cyborgcnc/CYBORGCNC__RRVC3MOD/500x500/MARCEL-Remix-MODS/Top-Lid/README.md

<p align="center">
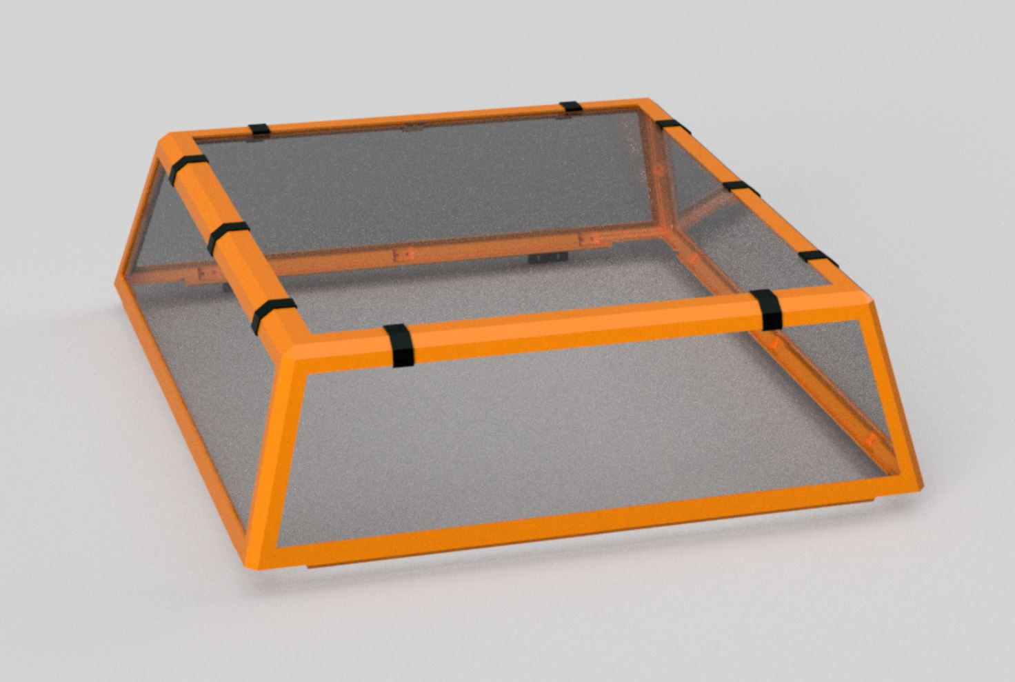
[picture p42: 500x500/MARCEL-Remix-MODS/Top-Lid/500_TopLid.JPG]

</p>
