cyborgcnc/CYBORGCNC__RRVC3MOD/400x400/HCOMB-Russel-Remix/IMG_20210630_090853.JPG

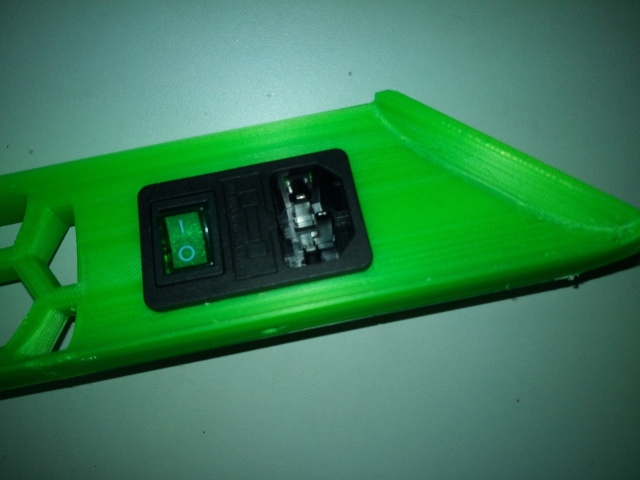
400x400/HCOMB-Russel-Remix/IMG_20210630_090853.JPG
