cyborgcnc/CYBORGCNC__RRVC3MOD/Activated-Carbon-Filter/Filter1.JPG

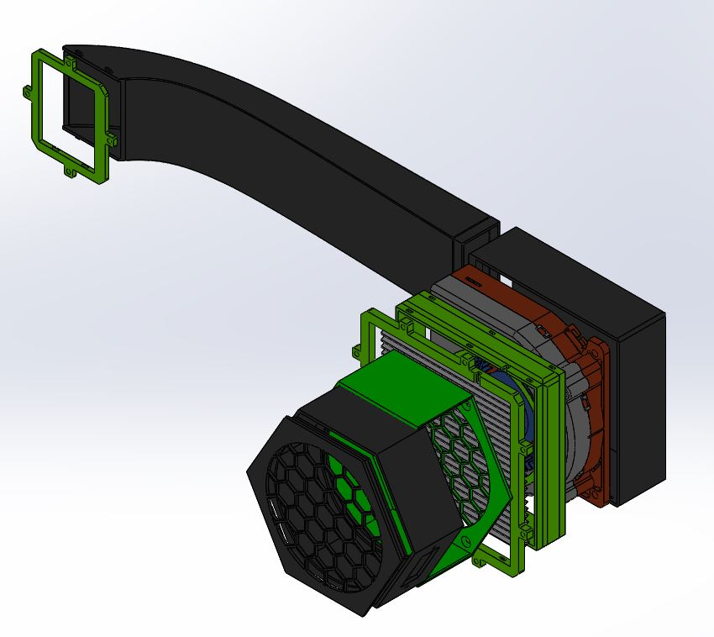
Activated-Carbon-Filter/Filter1.JPG
