cyborgcnc/CYBORGCNC__RRVC3MOD/Activated-Carbon-Filter/Filter3.JPG

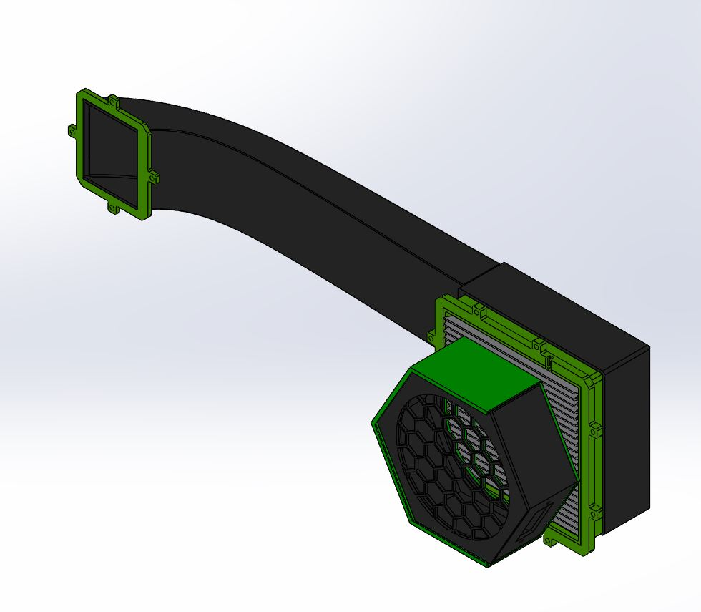
Activated-Carbon-Filter/Filter3.JPG
