cyborgcnc/CYBORGCNC__RRVC3MOD/CAN_Bus/SHT42.jpg

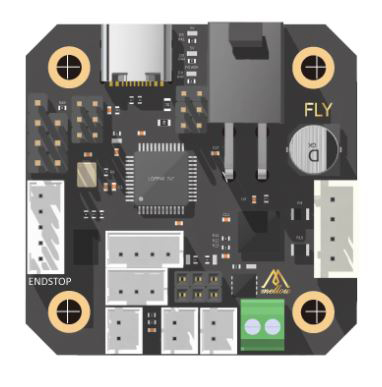
CAN_Bus/SHT42.jpg
