cyborgcnc/CYBORGCNC__RRVC3MOD/SpoolHolder-Inside/IMG_7930.jpg

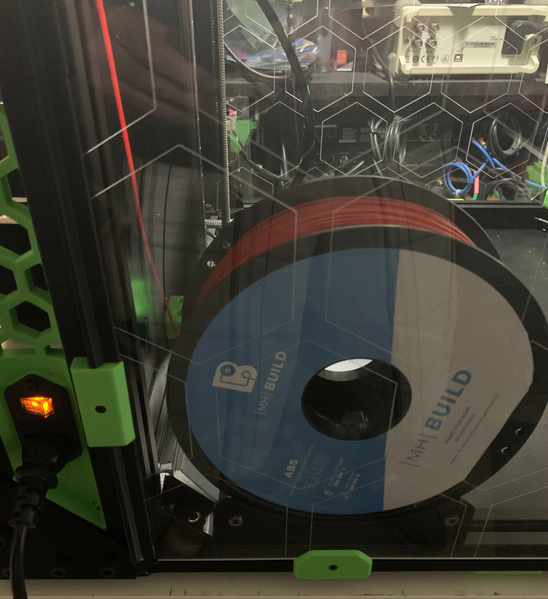
SpoolHolder-Inside/IMG_7930.jpg
