cyborgcnc/CYBORGCNC__RRVC3MOD/SpoolHolder-Inside/Spool2.JPG

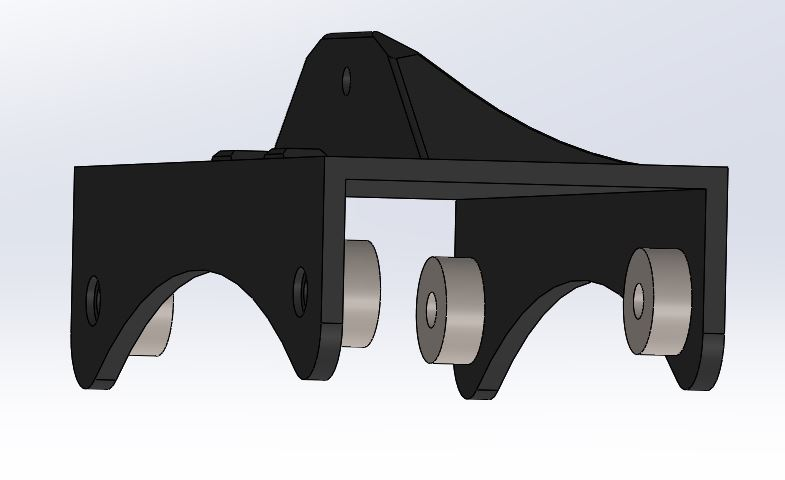
SpoolHolder-Inside/Spool2.JPG
