cyborgcnc/CYBORGCNC__RRVC3MOD/SpoolHolder-Inside/Spool4.JPG

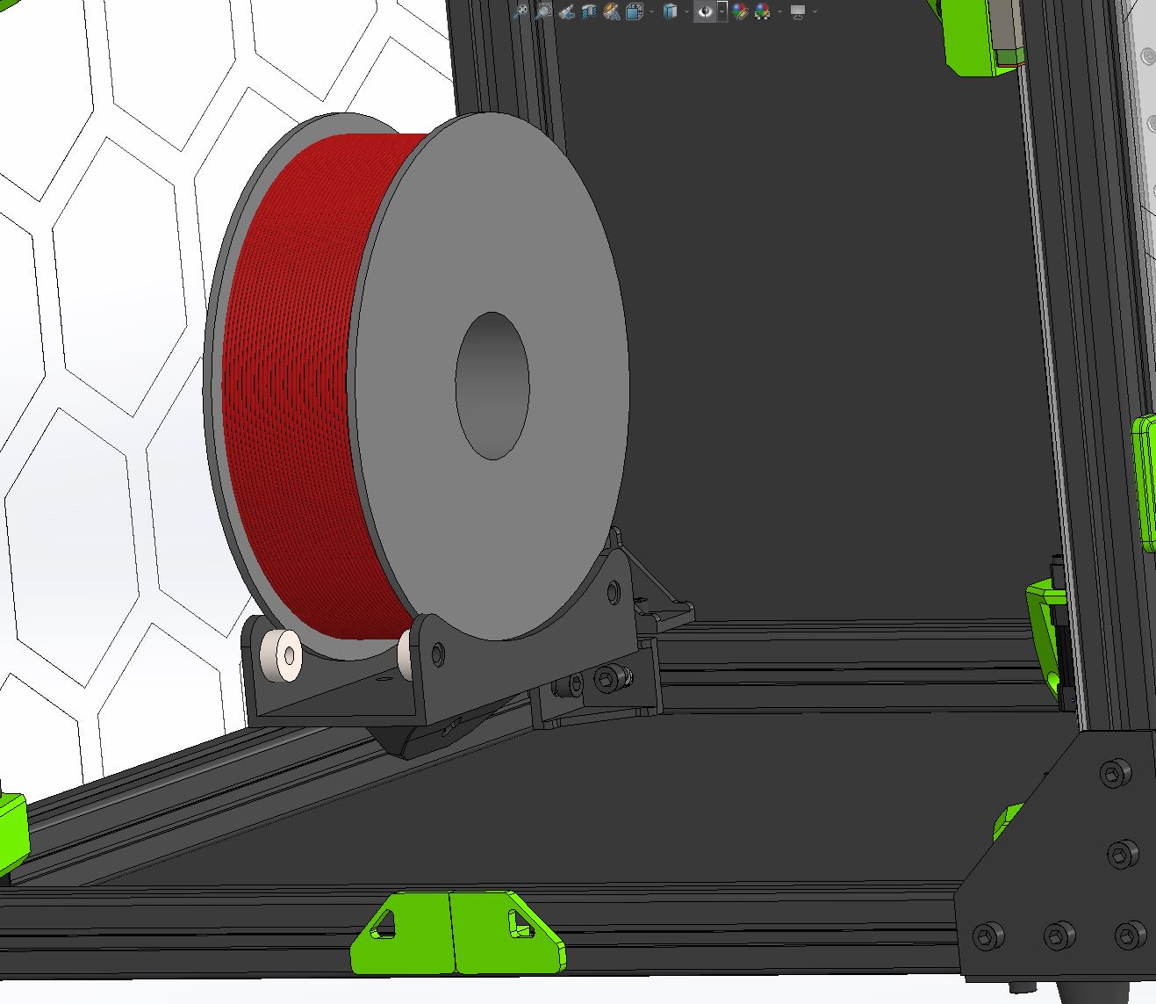
SpoolHolder-Inside/Spool4.JPG
