cyborgcnc/CYBORGCNC__RRVC3MOD/Activated-Carbon-Filter/Air-Duct-Internal.STEP

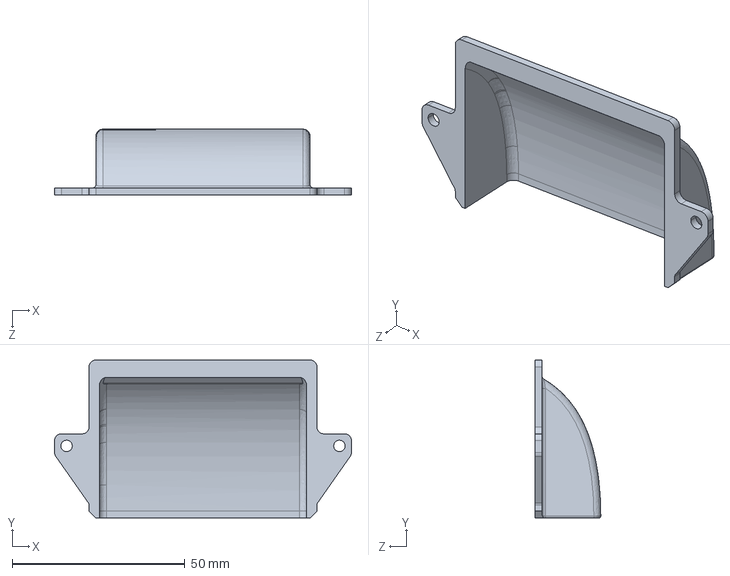
[picture p65: CAD file, 2022-03-03]
Activated-Carbon-Filter/Air-Duct-Internal.STEP
86.0 x 45.7 x 19.0 mm
