cyborgcnc/CYBORGCNC__RRVC3MOD/CAN_Bus/Cable-Holder-V4.STEP.STL

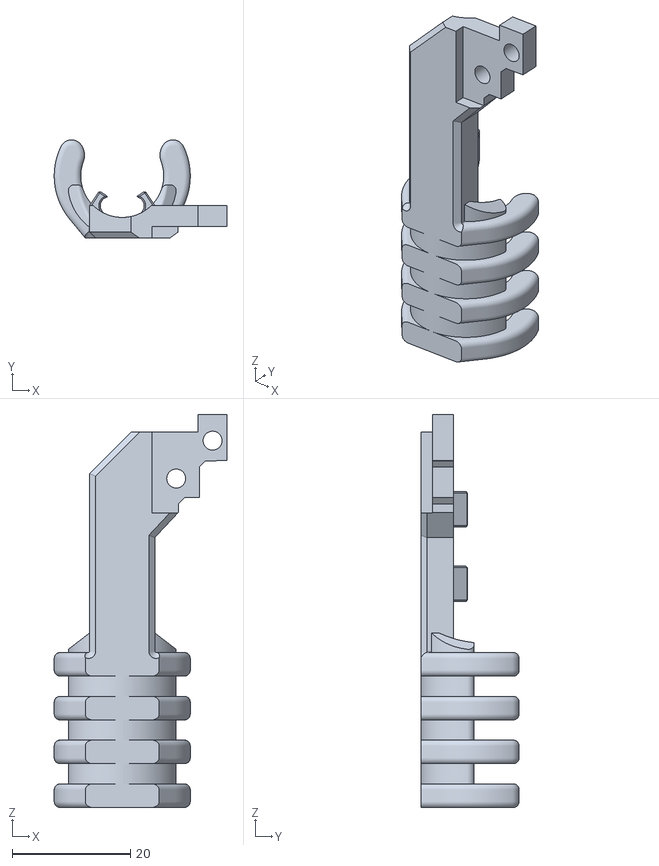
[picture p66: CAD file, 2022-04-21]
CAN_Bus/Cable-Holder-V4.STEP.STL
29.2 x 16.6 x 66.4
