cyborgcnc/CYBORGCNC__RRVC3MOD/LCD-MOUNT/BTT-Pi-TFT-CASE-Back.STEP

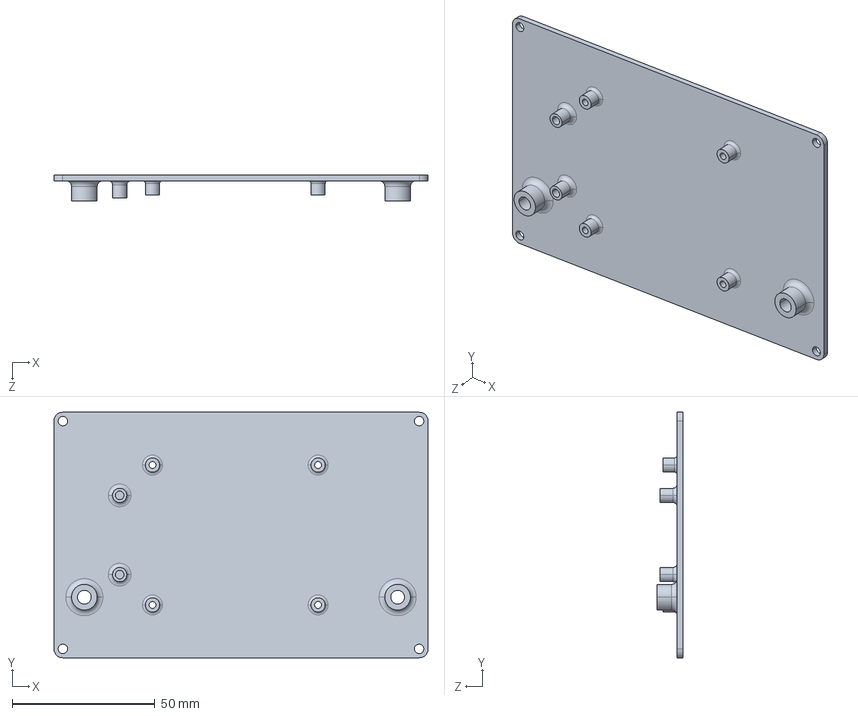
[picture p67: CAD file, 2021-09-12]
LCD-MOUNT/BTT-Pi-TFT-CASE-Back.STEP
131.0 x 86.0 x 9.00 mm
