cyborgcnc/CYBORGCNC__RRVC3MOD/Misc/120-mount-3030.STEP

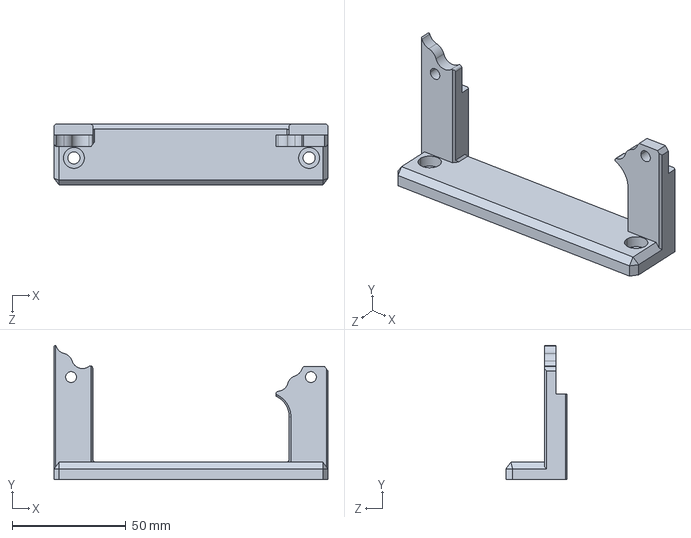
[picture p68: CAD file, 2023-03-15]
Misc/120-mount-3030.STEP
120.3 x 58.9 x 27.0 mm
