cyborgcnc/CYBORGCNC__RRVC3MOD/SpoolHolder-Inside/Spool-HolderV4.STEP

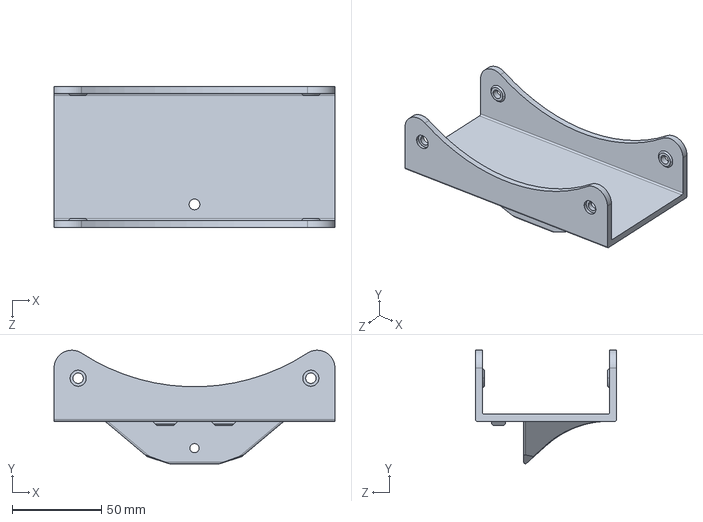
[picture p69: CAD file, 2021-08-01]
SpoolHolder-Inside/Spool-HolderV4.STEP
157.0 x 63.5 x 79.0 mm
