cyborgcnc/CYBORGCNC__RRVC3MOD/300x300/HCOMB-SIDES/HCOMB-RIGHT.300mm.STEP

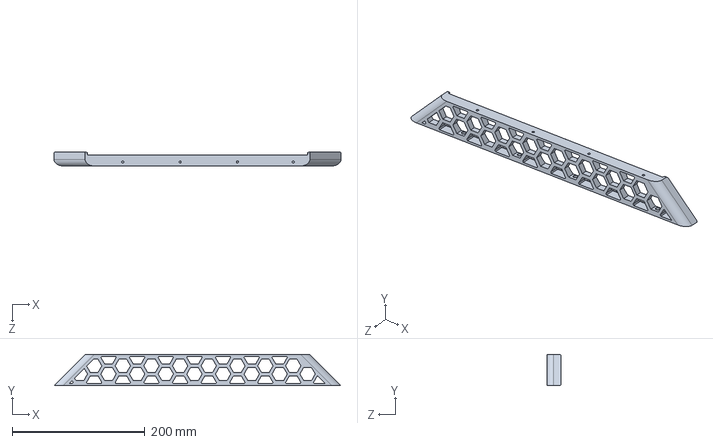
[picture p70: CAD file, 2021-07-01]
300x300/HCOMB-SIDES/HCOMB-RIGHT.300mm.STEP
431.7 x 46.8 x 21.0 mm
