cyborgcnc/CYBORGCNC__RRVC3MOD/400x400/Door-Hinge-Right.STEP

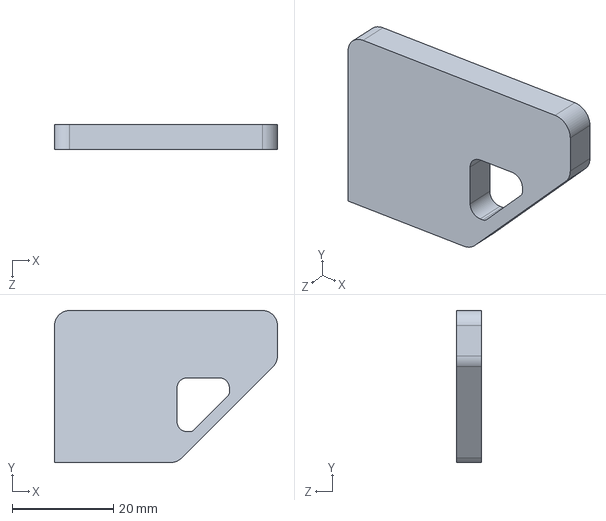
[picture p71: CAD file, 2021-10-21]
400x400/Door-Hinge-Right.STEP
44.0 x 30.0 x 5.00 mm
