cyborgcnc/CYBORGCNC__RRVC3MOD/400x400/HCOMB-Russel-Remix/Back-Hcomb-Left-Half2-IEC.step

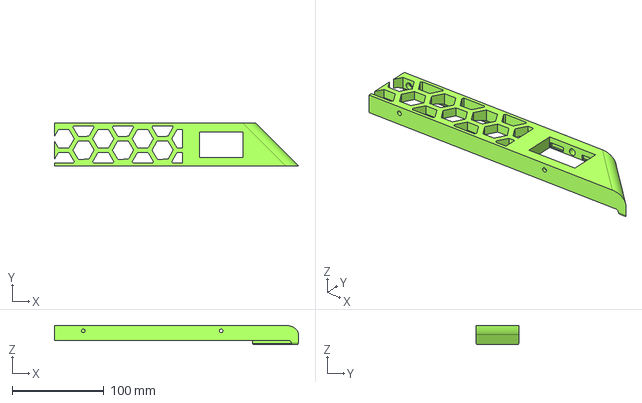
[picture p72: CAD file, 2021-06-30]
400x400/HCOMB-Russel-Remix/Back-Hcomb-Left-Half2-IEC.step
265.9 x 46.8 x 21.0 mm
