cyborgcnc/CYBORGCNC__RRVC3MOD/400x400/Panels/BACK-Electronics-Top-Cover.STEP

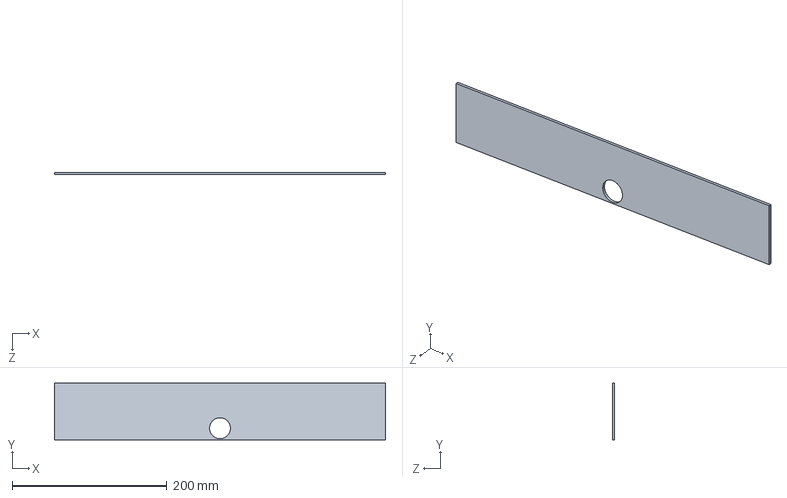
[picture p73: CAD file, 2021-07-21]
400x400/Panels/BACK-Electronics-Top-Cover.STEP
428.0 x 73.3 x 3.17 mm
