cyborgcnc/CYBORGCNC__RRVC3MOD/400x400/Sides-HoneyComb/Back-Hcomb-Left.STEP

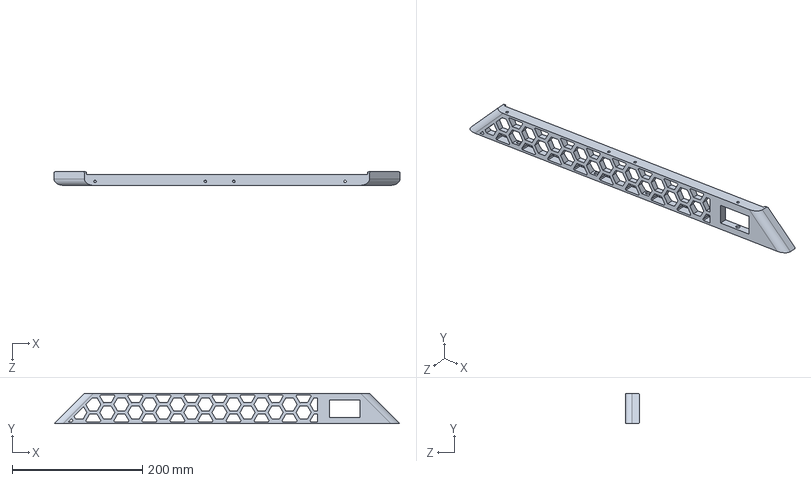
[picture p74: CAD file, 2021-06-17]
400x400/Sides-HoneyComb/Back-Hcomb-Left.STEP
531.7 x 46.8 x 21.0 mm
