cyborgcnc/CYBORGCNC__RRVC3MOD/400x400/TOP-LID/Lid-Side-Panel-SIDES.STEP

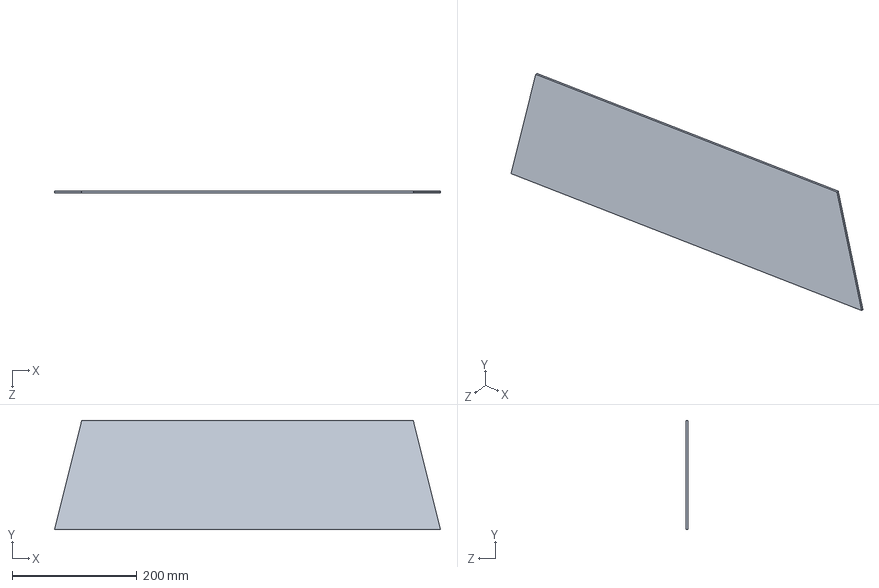
[picture p75: CAD file, 2021-07-27]
400x400/TOP-LID/Lid-Side-Panel-SIDES.STEP
618.1 x 174.7 x 3.12 mm
