cyborgcnc/CYBORGCNC__RRVC3MOD/400x400/TOP-LID/STEP-FILES/Btm-Bar-FRONT.RIGHT-HALF.STEP

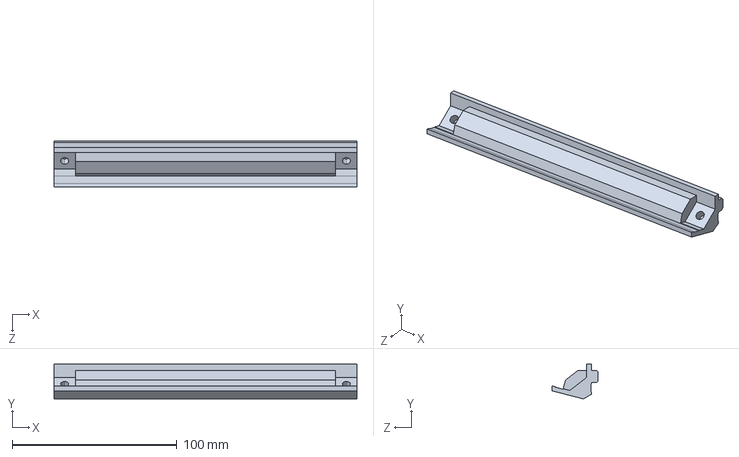
[picture p76: CAD file, 2021-07-08]
400x400/TOP-LID/STEP-FILES/Btm-Bar-FRONT.RIGHT-HALF.STEP
183.8 x 21.2 x 27.9 mm
