cyborgcnc/CYBORGCNC__RRVC3MOD/500x500/HCOMB-SIDES/hcomb.LEFT.500mm.STEP

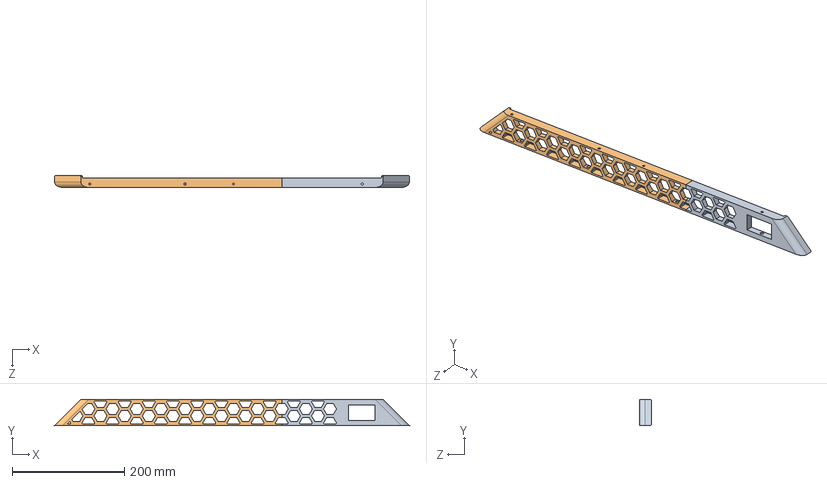
[picture p77: CAD file, 2021-06-30]
500x500/HCOMB-SIDES/hcomb.LEFT.500mm.STEP
632.7 x 46.8 x 21.0 mm
BACK-SIDE-Panels.LEFT.500-part1
BACK-SIDE-Panels.LEFT.500-part2
