cyborgcnc/CYBORGCNC__RRVC3MOD/500x500/MARCEL-Remix-MODS/Panels/Handels v2.step

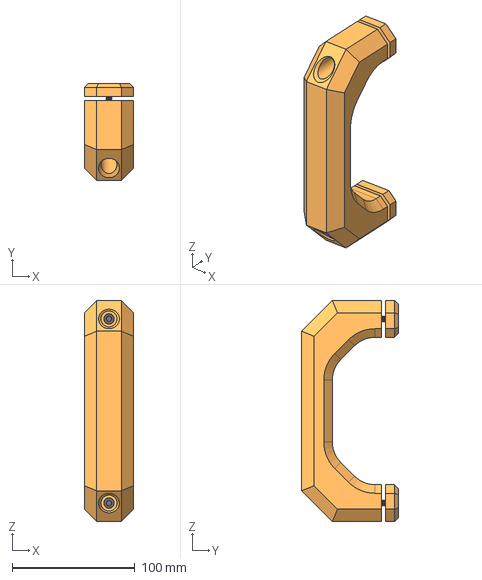
[picture p78: CAD file, 2021-09-10]
500x500/MARCEL-Remix-MODS/Panels/Handels v2.step
40.0 x 78.7 x 180.0 mm
M5x12 x 2
