cyborgcnc/CYBORGCNC__RRVC3MOD/500x500/MARCEL-Remix-MODS/Top-Lid/500_TopLid_Top.dxf

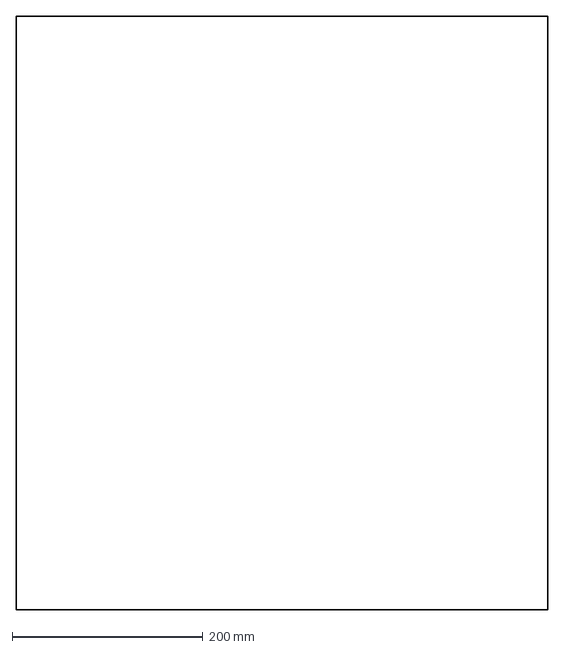
[picture p79: CAD file, 2021-09-10]
500x500/MARCEL-Remix-MODS/Top-Lid/500_TopLid_Top.dxf
558.0 x 623.0 mm
