cyborgcnc/CYBORGCNC__RRVC3MOD/Activated-Carbon-Filter/Small-Mounting-Bracket.STEP

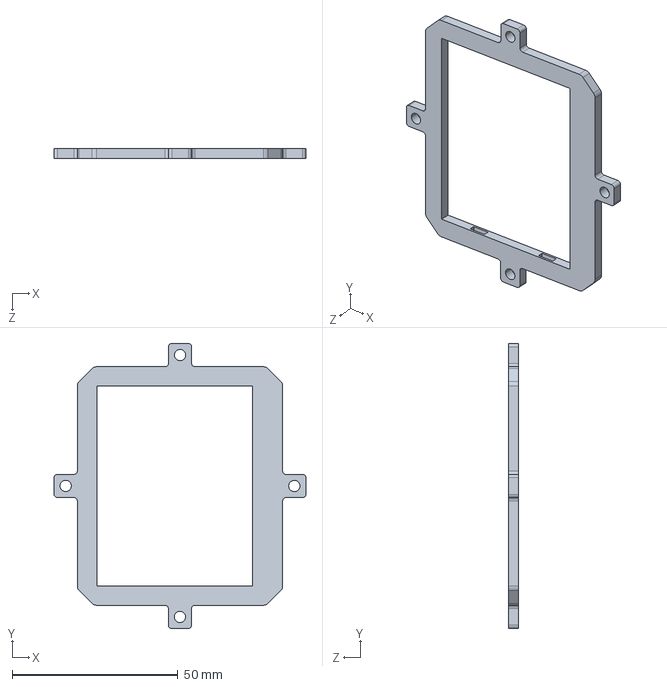
[picture p80: CAD file, 2021-07-02]
Activated-Carbon-Filter/Small-Mounting-Bracket.STEP
76.0 x 86.0 x 3.00 mm
