cyborgcnc/CYBORGCNC__RRVC3MOD/CAN_Bus/FAN-DUCT.STEP

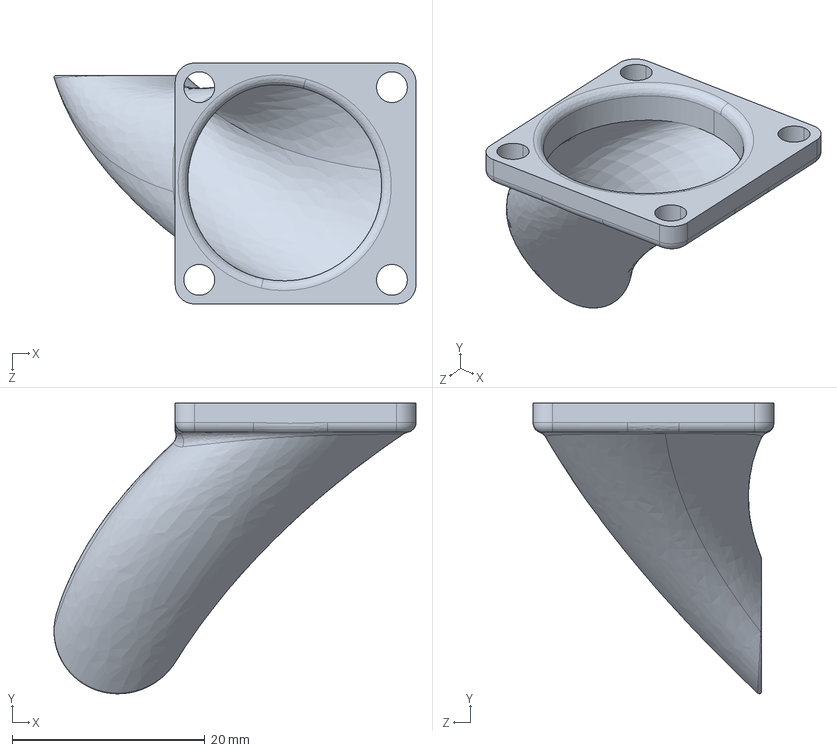
[picture p81: CAD file, 2022-04-21]
CAN_Bus/FAN-DUCT.STEP
37.6 x 30.2 x 25.0 mm
