cyborgcnc/CYBORGCNC__RRVC3MOD/LCD-MOUNT/LCD-Mount-Bracket.STEP

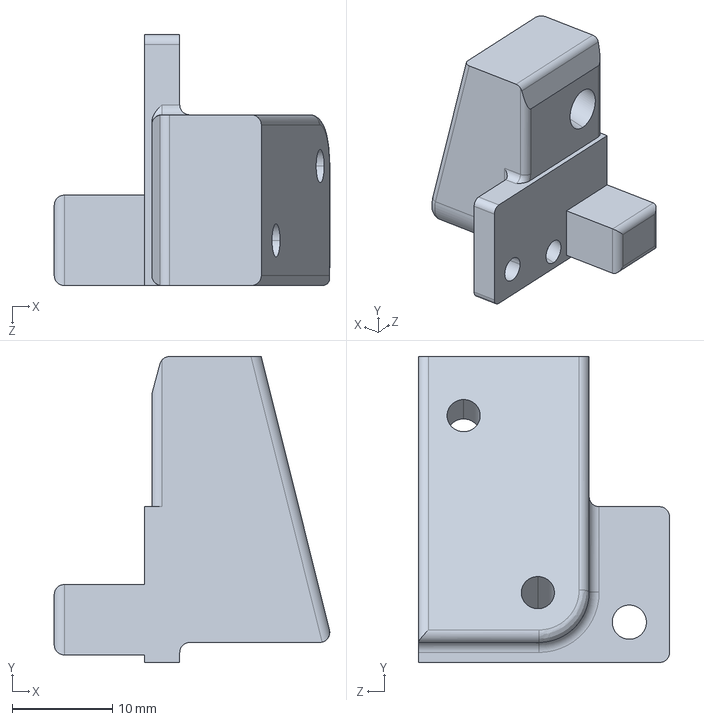
[picture p82: CAD file, 2021-09-12]
LCD-MOUNT/LCD-Mount-Bracket.STEP
27.4 x 30.5 x 25.0 mm
