cyborgcnc/CYBORGCNC__RRVC3MOD/Misc/Btt-Sensor-Mount.STL

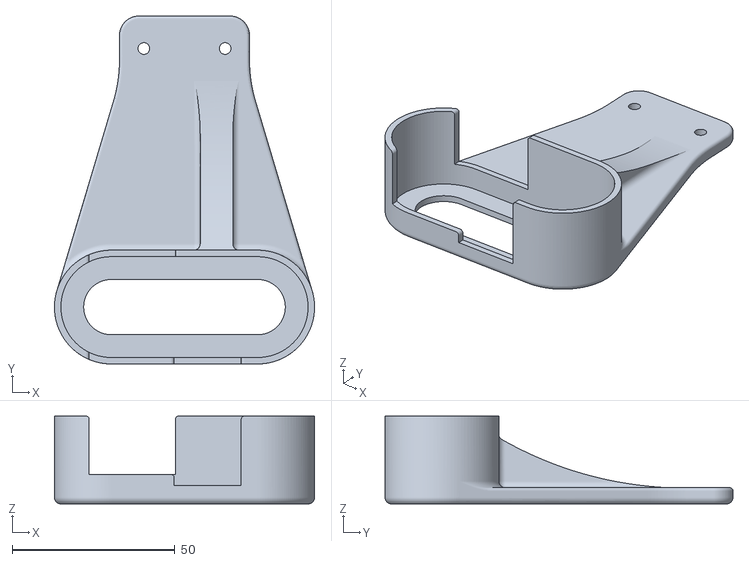
[picture p83: CAD file, 2023-02-15]
Misc/Btt-Sensor-Mount.STL
80.0 x 107.0 x 27.0
