cyborgcnc/CYBORGCNC__RRVC3MOD/400x400/Hinge-Front-Doors.STEP

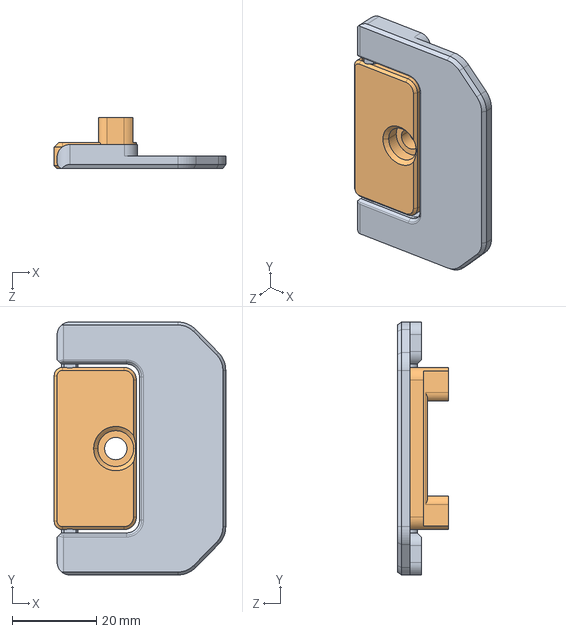
[picture p84: CAD file, 2021-09-24]
400x400/Hinge-Front-Doors.STEP
40.7 x 60.0 x 12.2 mm
