cyborgcnc/CYBORGCNC__RRVC3MOD/400x400/Panels/Front-Door.Panel.STEP

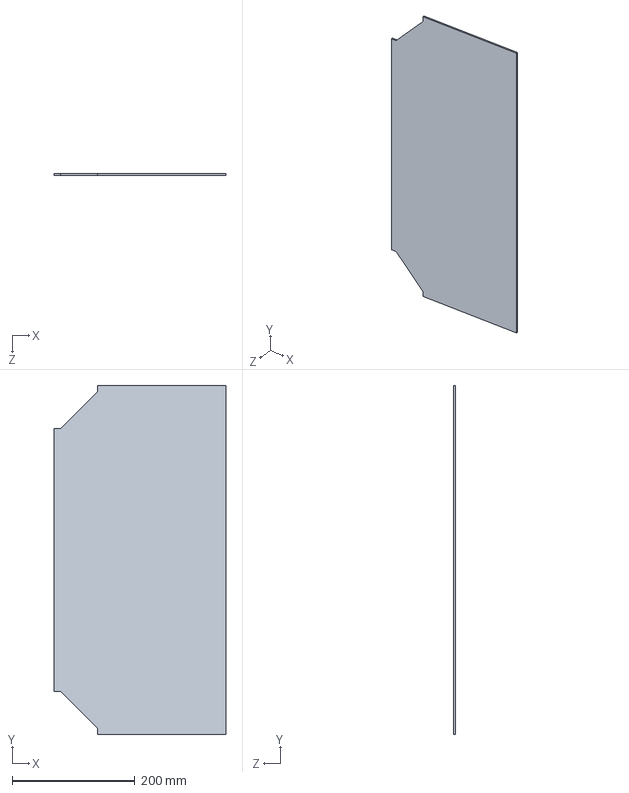
[picture p85: CAD file, 2021-07-21]
400x400/Panels/Front-Door.Panel.STEP
280.7 x 569.7 x 3.17 mm
