cyborgcnc/CYBORGCNC__RRVC3MOD/400x400/Sides-HoneyComb/Back-Hcomb-Left-Half2.STL

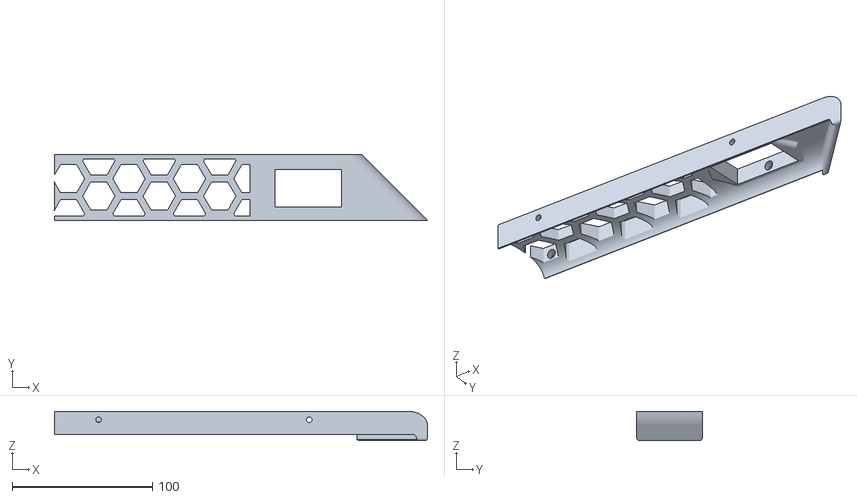
[picture p86: CAD file, 2021-06-17]
400x400/Sides-HoneyComb/Back-Hcomb-Left-Half2.STL
265.9 x 46.8 x 21.0
