cyborgcnc/CYBORGCNC__RRVC3MOD/400x400/TOP-LID/Lid-Side-Panel-FRONT-BACK.STEP

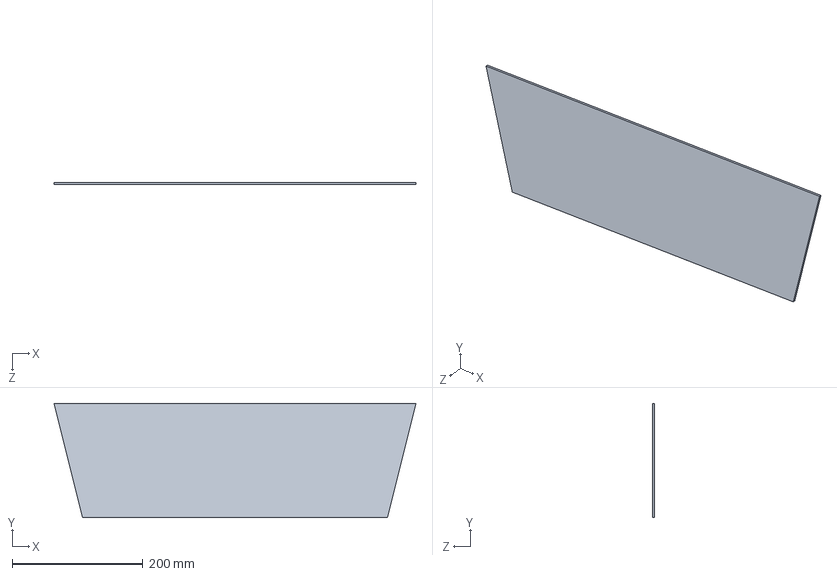
[picture p87: CAD file, 2021-07-27]
400x400/TOP-LID/Lid-Side-Panel-FRONT-BACK.STEP
553.1 x 174.7 x 3.12 mm
