cyborgcnc/CYBORGCNC__RRVC3MOD/400x400/TOP-LID/STEP-FILES/Btm-Back-LEFT-Corner.V6.20mm.STEP

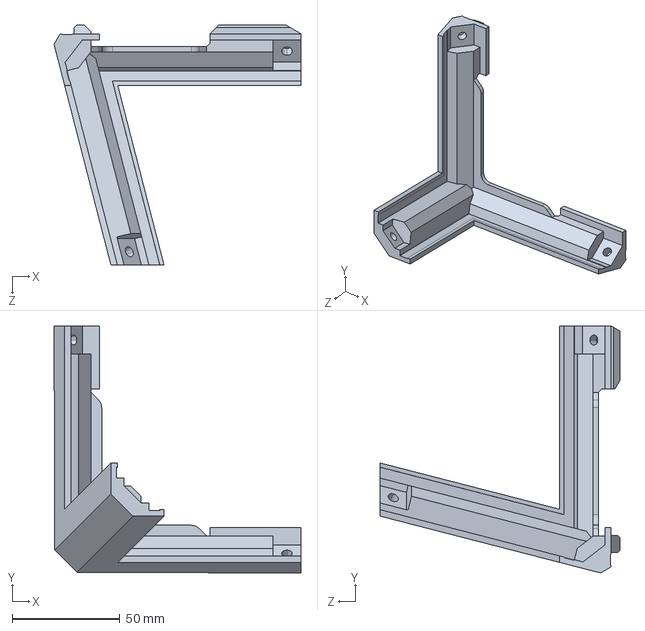
[picture p88: CAD file, 2021-07-08]
400x400/TOP-LID/STEP-FILES/Btm-Back-LEFT-Corner.V6.20mm.STEP
114.6 x 114.6 x 111.2 mm
