cyborgcnc/CYBORGCNC__RRVC3MOD/500x500/MARCEL-Remix-MODS/Panels/Pin.stl

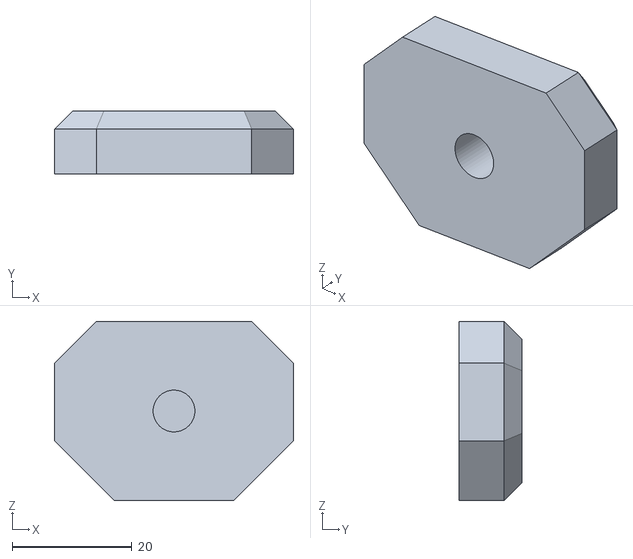
[picture p89: CAD file, 2021-09-10]
500x500/MARCEL-Remix-MODS/Panels/Pin.stl
40.0 x 10.5 x 30.0
