cyborgcnc/CYBORGCNC__RRVC3MOD/500x500/MARCEL-Remix-MODS/Top-Lid/Top-Bar-374mmx2 v2.stl

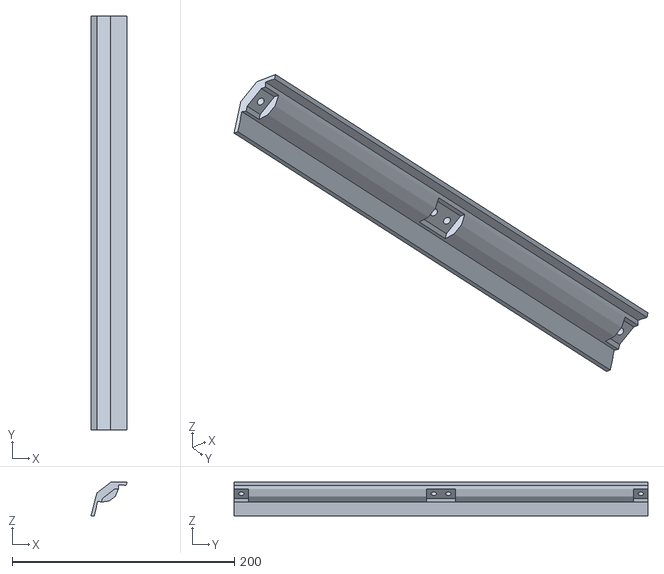
[picture p90: CAD file, 2021-09-10]
500x500/MARCEL-Remix-MODS/Top-Lid/Top-Bar-374mmx2 v2.stl
32.4 x 372.4 x 30.2
