cyborgcnc/CYBORGCNC__RRVC3MOD/Activated-Carbon-Filter/Filter-Duct.STEP

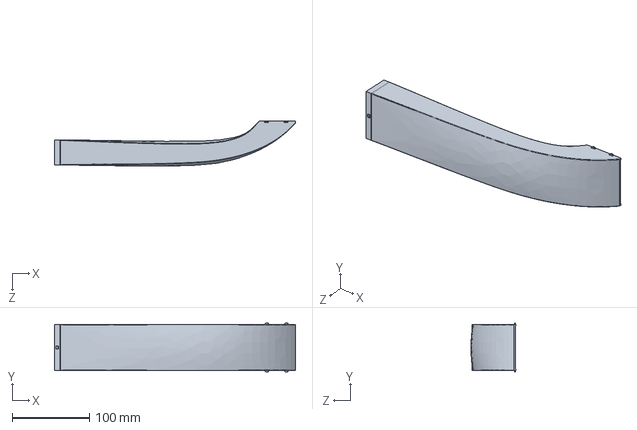
[picture p91: CAD file, 2021-07-02]
Activated-Carbon-Filter/Filter-Duct.STEP
311.9 x 63.0 x 58.5 mm
