cyborgcnc/CYBORGCNC__RRVC3MOD/CAN_Bus/SHt42-Mount-Angled.STEP

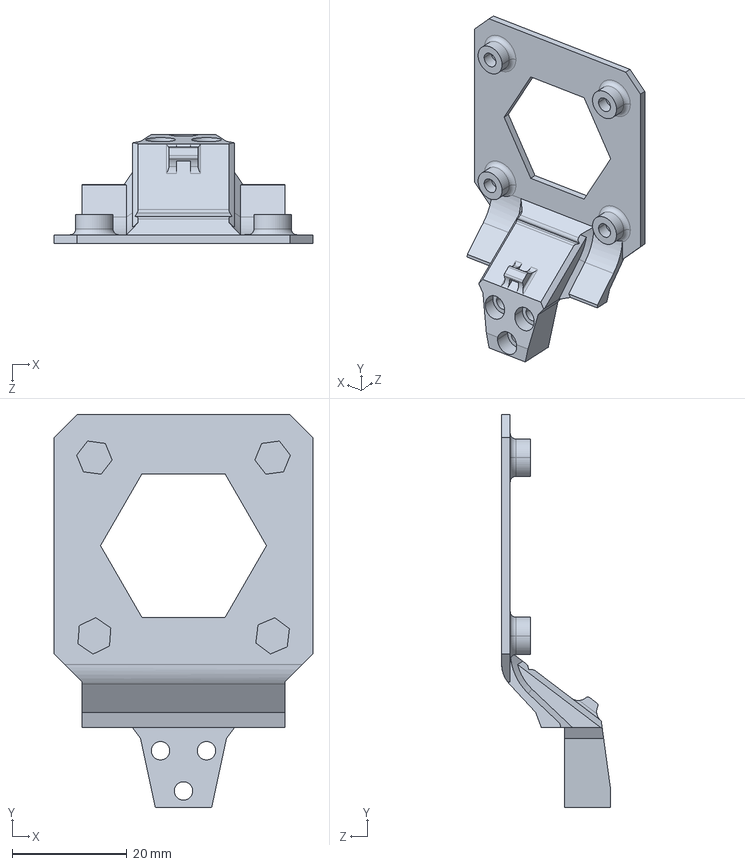
[picture p92: CAD file, 2022-04-21]
CAN_Bus/SHt42-Mount-Angled.STEP
45.0 x 68.4 x 18.9 mm
