cyborgcnc/CYBORGCNC__RRVC3MOD/LCD-MOUNT/Btt-TFT-Case-TOP.STEP

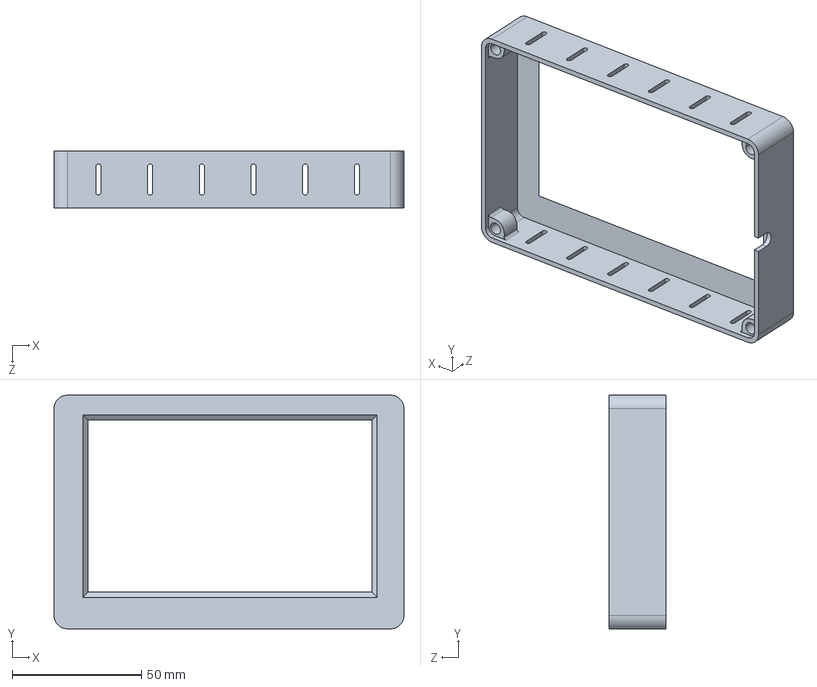
[picture p93: CAD file, 2021-09-12]
LCD-MOUNT/Btt-TFT-Case-TOP.STEP
135.4 x 90.4 x 22.0 mm
