cyborgcnc/CYBORGCNC__RRVC3MOD/Misc/eva-shroud-hcomb.STL

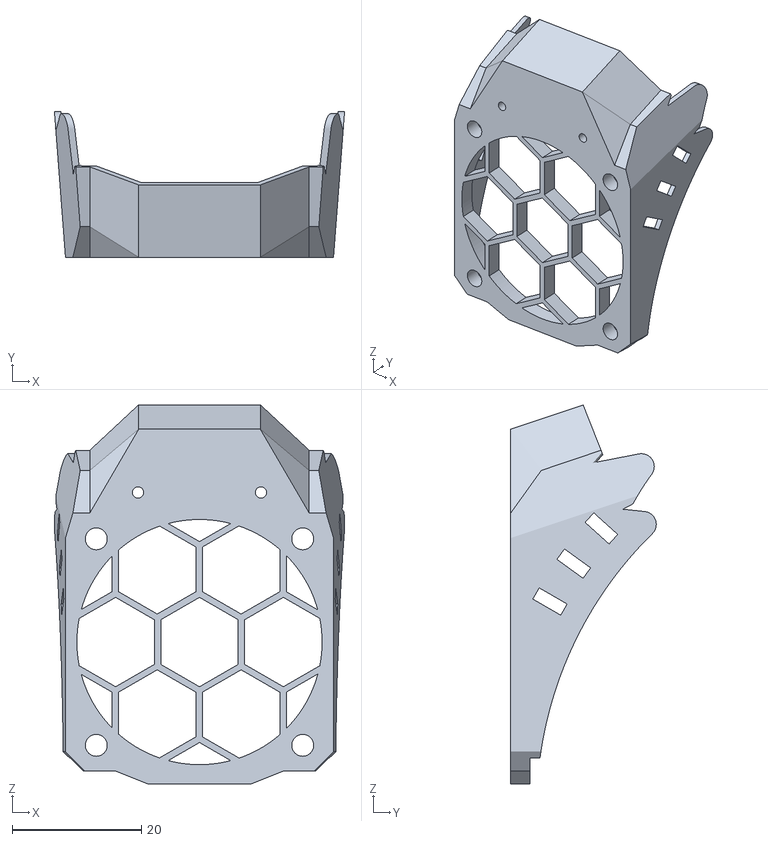
[picture p94: CAD file, 2021-11-10]
Misc/eva-shroud-hcomb.STL
45.0 x 22.6 x 58.7
