cyborgcnc/CYBORGCNC__RRVC3MOD/SpoolHolder-Inside/PTFE-Tube-Holder.STEP

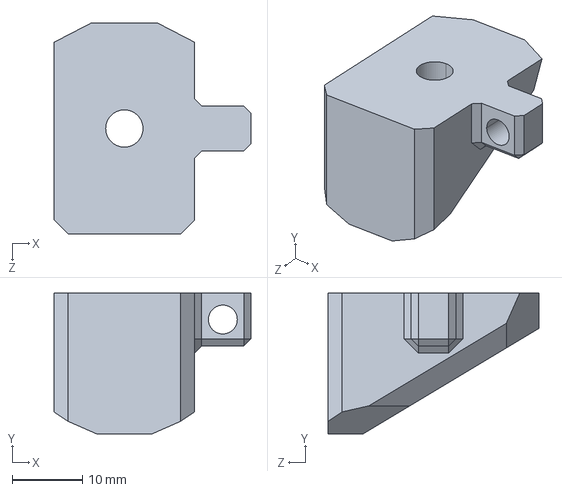
[picture p95: CAD file, 2021-08-01]
SpoolHolder-Inside/PTFE-Tube-Holder.STEP
28.0 x 20.0 x 30.0 mm
