cyborgcnc/CYBORGCNC__RRVC3MOD/400x400/LED-Clip.100mm.neopixel.STEP

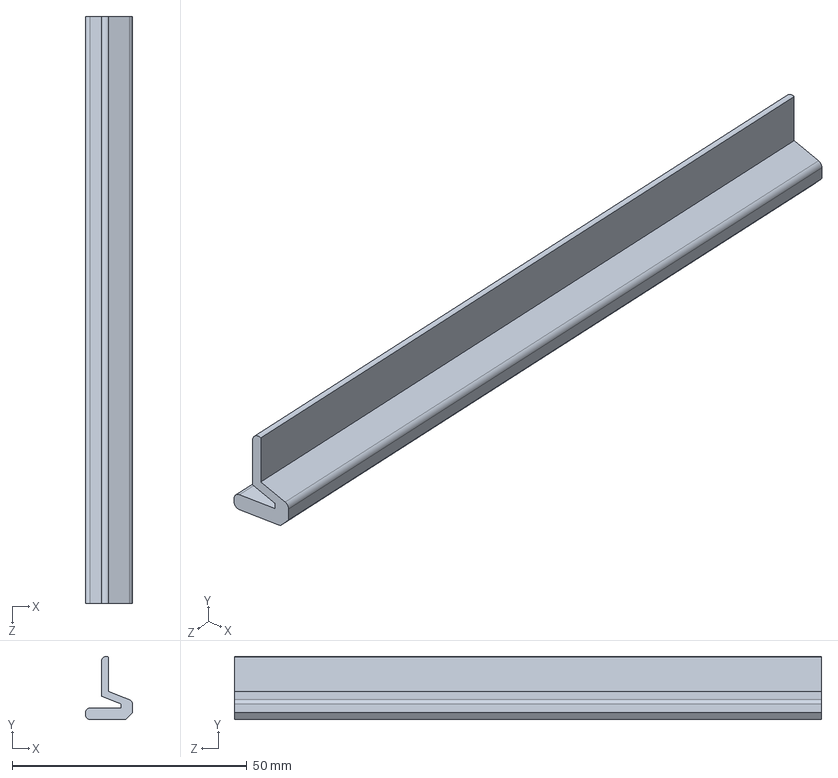
[picture p96: CAD file, 2021-07-08]
400x400/LED-Clip.100mm.neopixel.STEP
10.00 x 13.5 x 125.0 mm
