cyborgcnc/CYBORGCNC__RRVC3MOD/400x400/TOP-LID/SIDES-Clips-Joiners.STL

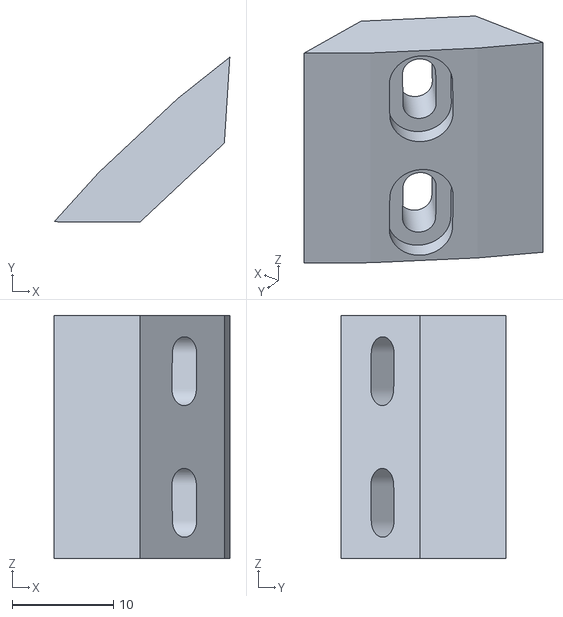
[picture p98: CAD file, 2021-06-28]
400x400/TOP-LID/SIDES-Clips-Joiners.STL
17.4 x 16.3 x 24.0
