cyborgcnc/CYBORGCNC__RRVC3MOD/400x400/TOP-LID/STEP-FILES/Top-Bar-274mm.STEP

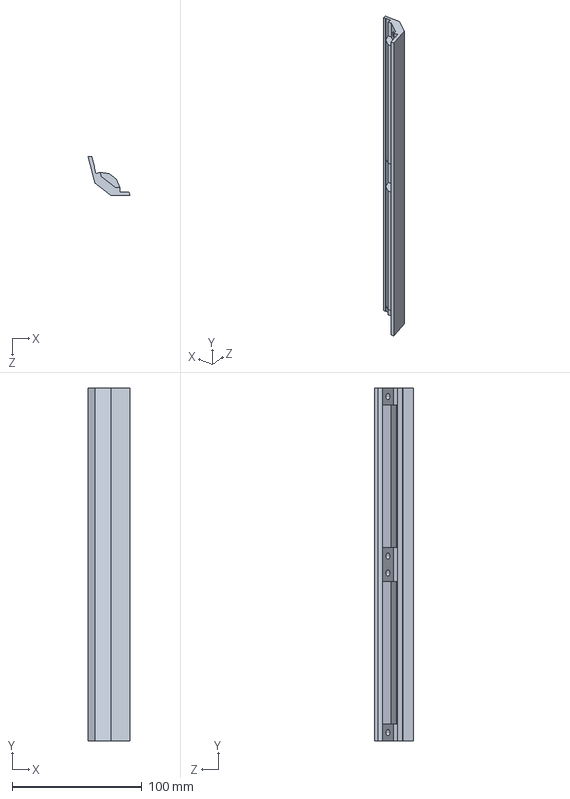
[picture p99: CAD file, 2021-07-08]
400x400/TOP-LID/STEP-FILES/Top-Bar-274mm.STEP
32.4 x 272.5 x 30.2 mm
