cyborgcnc/CYBORGCNC__RRVC3MOD/500x500/MARCEL-Remix-MODS/Panels/500_Doors.dxf

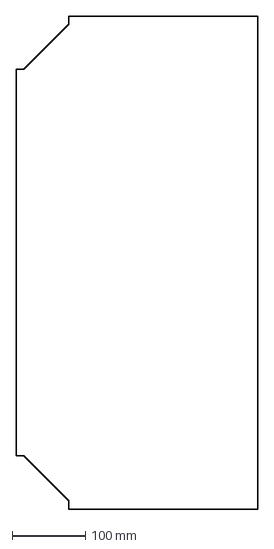
[picture p100: CAD file, 2021-09-10]
500x500/MARCEL-Remix-MODS/Panels/500_Doors.dxf
329.4 x 671.7 mm
