cyborgcnc/CYBORGCNC__RRVC3MOD/500x500/MARCEL-Remix-MODS/Top-Lid/500_Top-Bar_Sides_HALF v2.stl

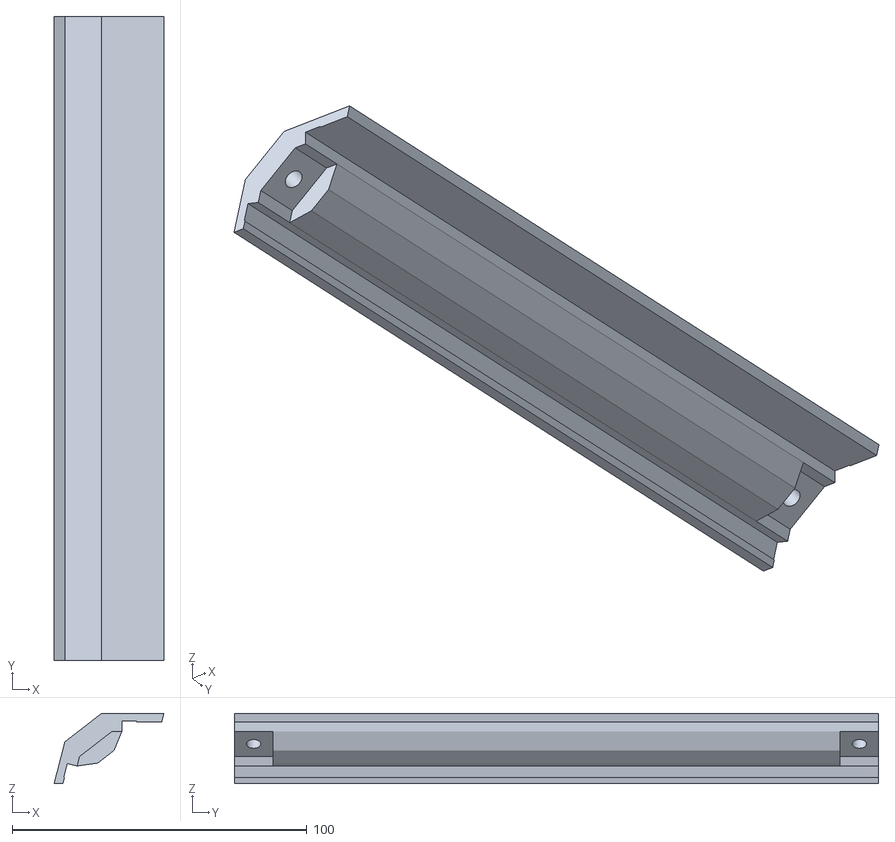
[picture p101: CAD file, 2021-09-10]
500x500/MARCEL-Remix-MODS/Top-Lid/500_Top-Bar_Sides_HALF v2.stl
37.3 x 218.7 x 23.9
