cyborgcnc/CYBORGCNC__RRVC3MOD/Activated-Carbon-Filter/Catridge-Top-Lid.STEP

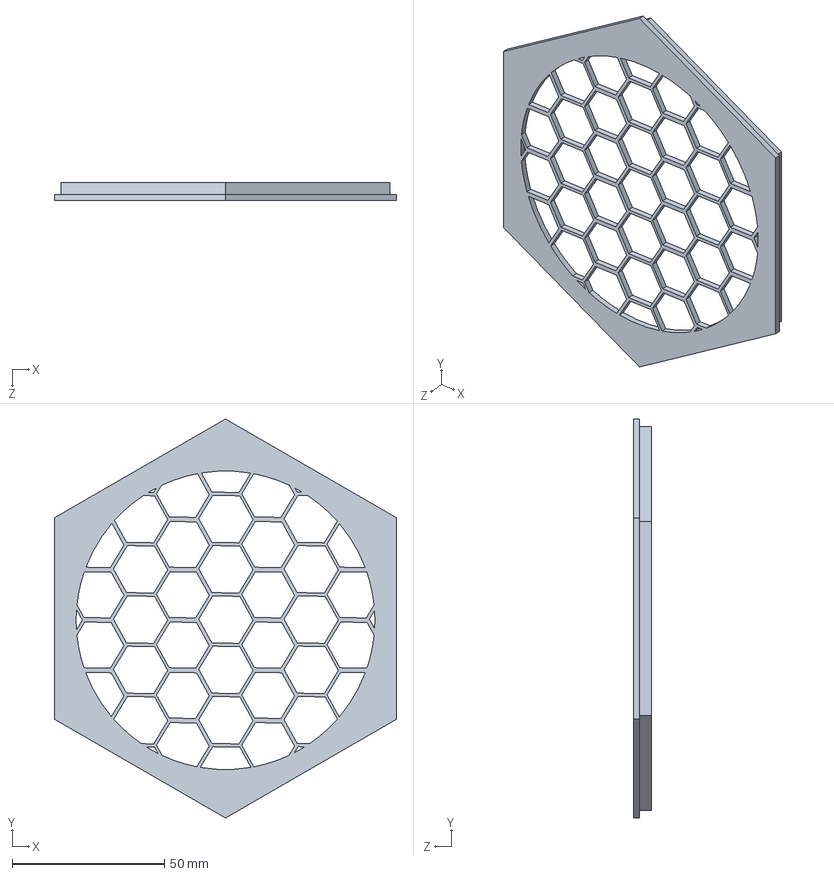
[picture p102: CAD file, 2021-07-02]
Activated-Carbon-Filter/Catridge-Top-Lid.STEP
112.4 x 130.9 x 6.00 mm
