cyborgcnc/CYBORGCNC__RRVC3MOD/CAN_Bus/sht42-TOP-Cover.STL

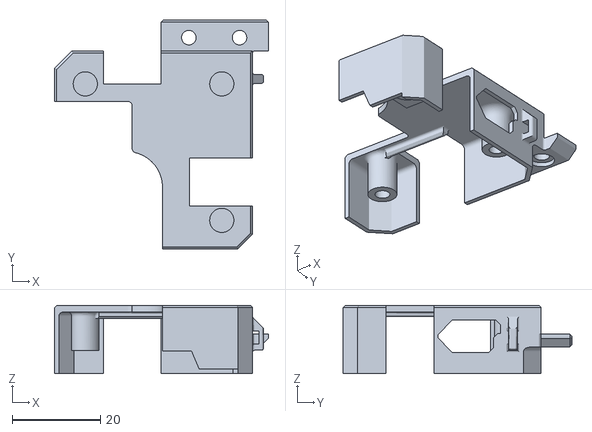
[picture p103: CAD file, 2022-04-21]
CAN_Bus/sht42-TOP-Cover.STL
48.6 x 52.0 x 15.5
