cyborgcnc/CYBORGCNC__RRVC3MOD/Misc/eva-shroud-dragon.STL

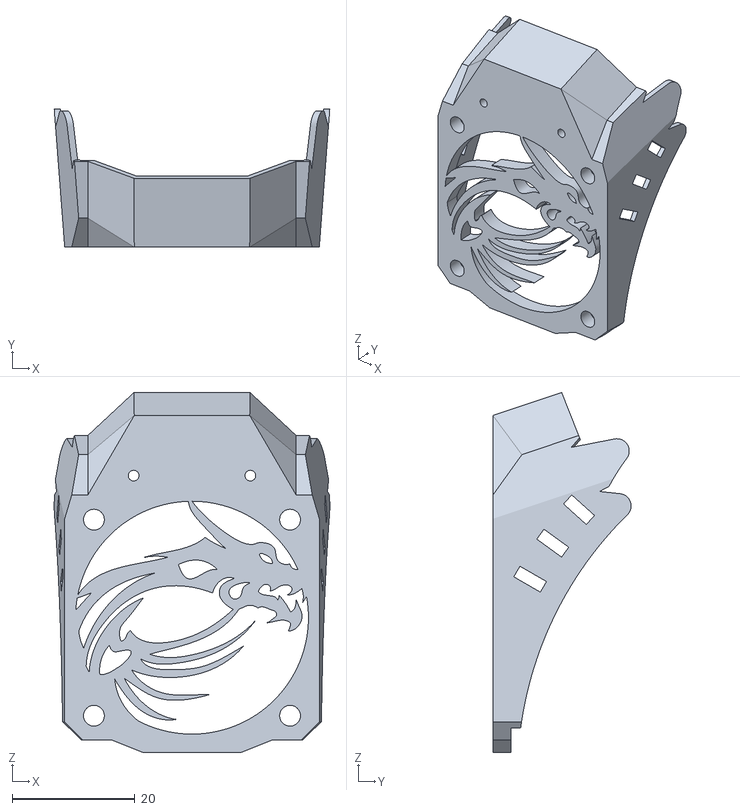
[picture p104: CAD file, 2021-11-10]
Misc/eva-shroud-dragon.STL
45.0 x 22.6 x 58.7
