cyborgcnc/CYBORGCNC__RRVC3MOD/WOBBLE-RINGS/Bed-Arms-Wobble-Ring.FRONT.STEP

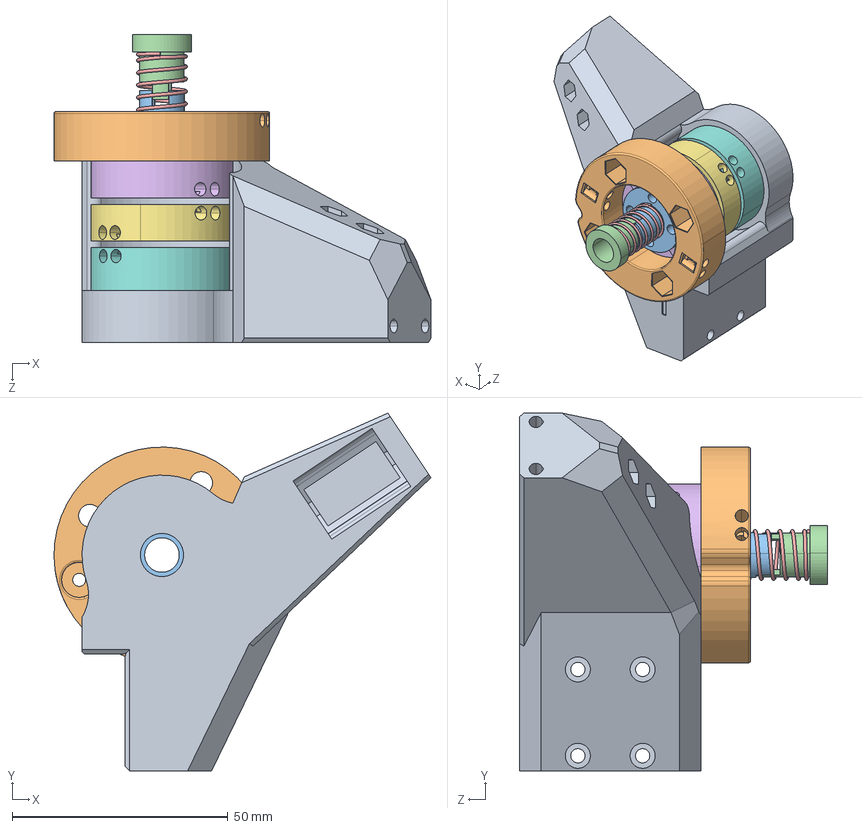
[picture p105: CAD file, 2021-07-24]
WOBBLE-RINGS/Bed-Arms-Wobble-Ring.FRONT.STEP
87.3 x 82.9 x 71.3 mm
bed_arm_left .RING-Version
WobbleRings-_BTM
TR08
W-Ring-BTM-V2
W-Ring-MIDDLE-V2
W-Ring-TOP-V2
