cyborgcnc/CYBORGCNC__RRVC3MOD/400x400/ADXL-Mount.STL

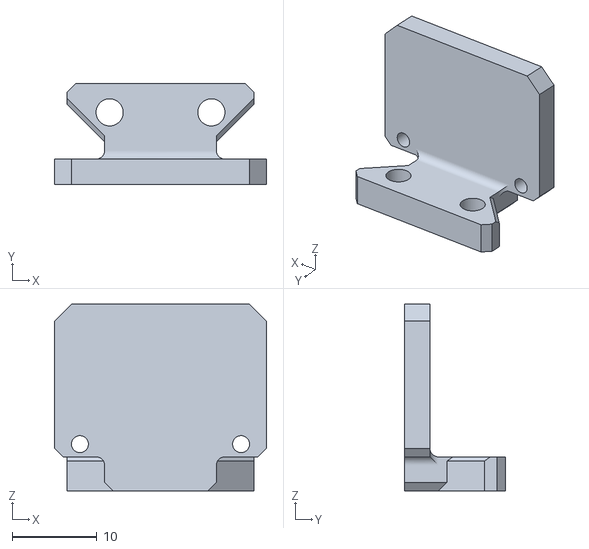
[picture p106: CAD file, 2021-06-20]
400x400/ADXL-Mount.STL
25.0 x 11.9 x 22.0
