cyborgcnc/CYBORGCNC__RRVC3MOD/400x400/Panels/BTM-Panel-V2.STL

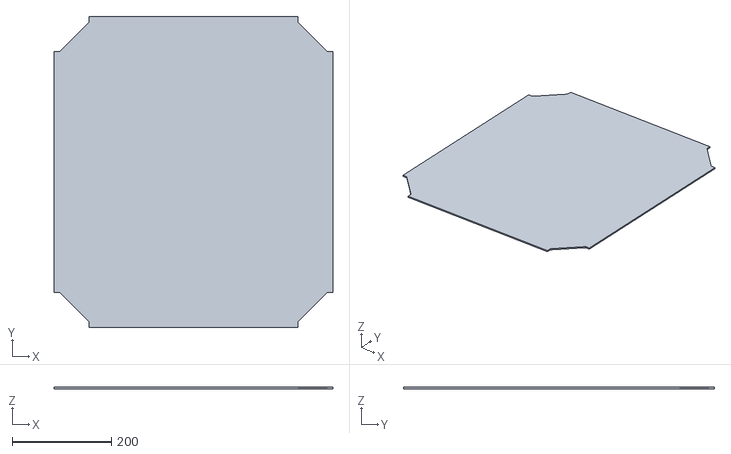
[picture p107: CAD file, 2021-06-25]
400x400/Panels/BTM-Panel-V2.STL
561.7 x 626.7 x 3.12
