cyborgcnc/CYBORGCNC__RRVC3MOD/400x400/TOP-LID/TOP-Clips-Joiners.STL

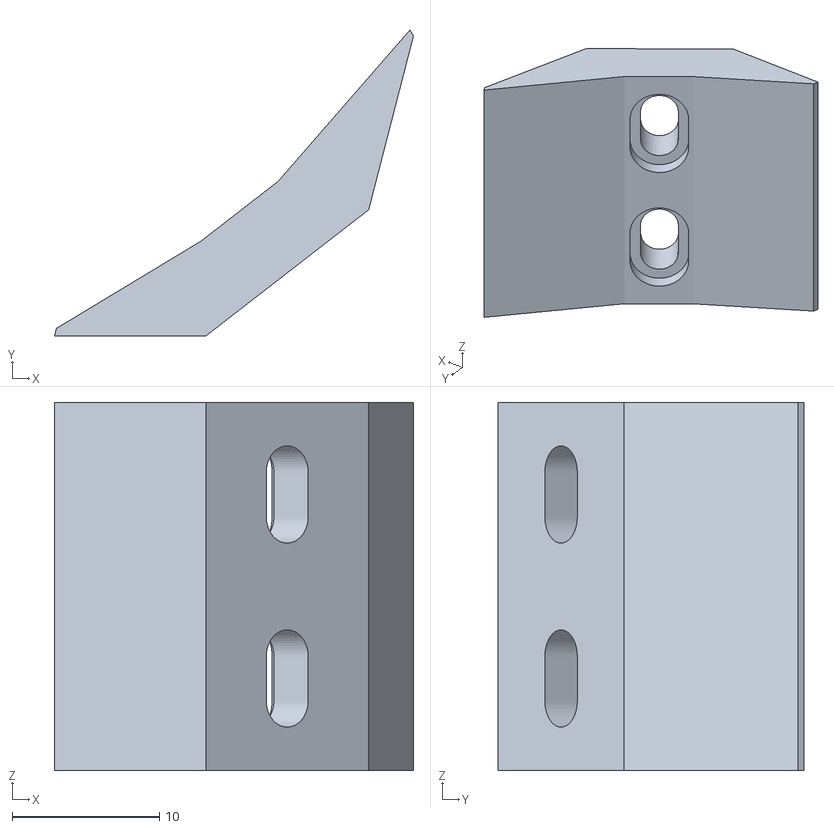
[picture p108: CAD file, 2021-06-28]
400x400/TOP-LID/TOP-Clips-Joiners.STL
24.4 x 20.8 x 25.0
