cyborgcnc/CYBORGCNC__RRVC3MOD/500x500/MARCEL-Remix-MODS/Panels/500_Bottom.dxf

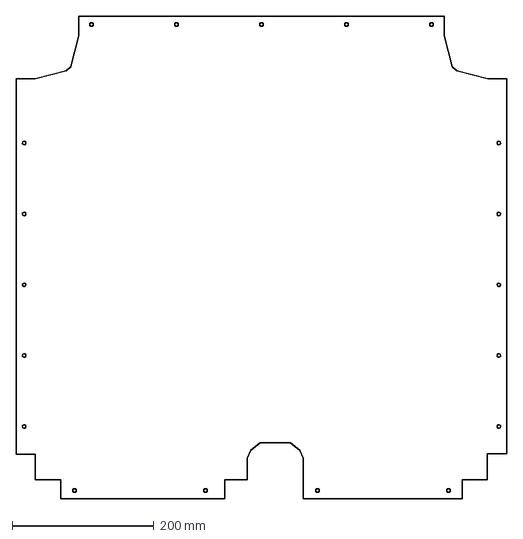
[picture p109: CAD file, 2021-09-10]
500x500/MARCEL-Remix-MODS/Panels/500_Bottom.dxf
693.0 x 681.0 mm
