cyborgcnc/CYBORGCNC__RRVC3MOD/500x500/MARCEL-Remix-MODS/Top-Lid/500_Btm-Bar-BACK.LEFT-HALF.stl

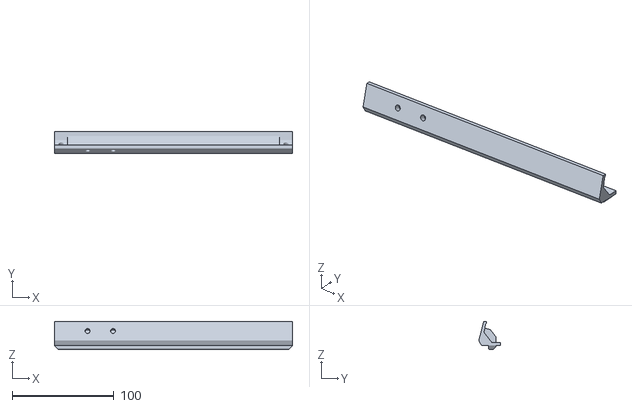
[picture p110: CAD file, 2021-09-10]
500x500/MARCEL-Remix-MODS/Top-Lid/500_Btm-Bar-BACK.LEFT-HALF.stl
233.8 x 21.2 x 27.9
