cyborgcnc/CYBORGCNC__RRVC3MOD/Activated-Carbon-Filter/BTM.Retainer.Ring.STEP

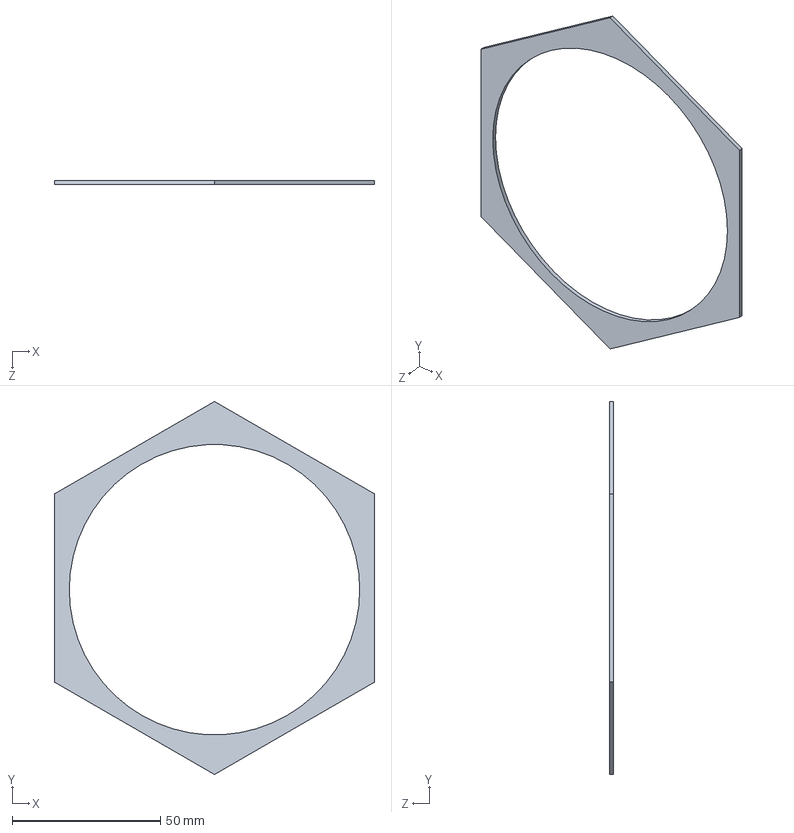
[picture p111: CAD file, 2021-07-02]
Activated-Carbon-Filter/BTM.Retainer.Ring.STEP
108.0 x 125.9 x 1.50 mm
