cyborgcnc/CYBORGCNC__RRVC3MOD/CAN_Bus/FAN-25x7-MountingBracket.STEP

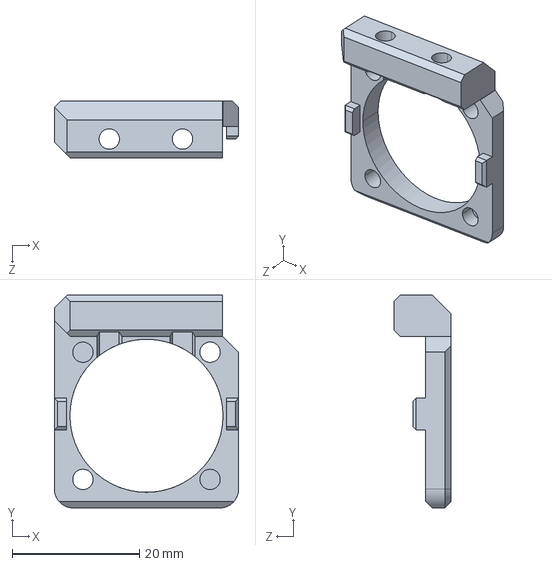
[picture p112: CAD file, 2022-04-21]
CAN_Bus/FAN-25x7-MountingBracket.STEP
29.0 x 33.5 x 9.00 mm
