cyborgcnc/CYBORGCNC__RRVC3MOD/WOBBLE-RINGS/W-Ring-MIDDLE-V2.STEP

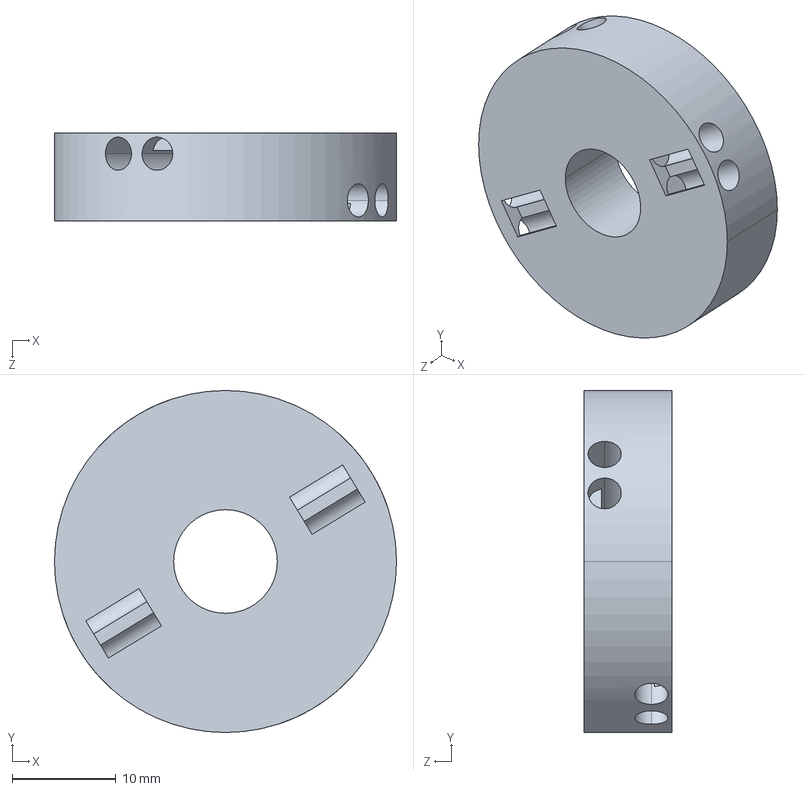
[picture p113: CAD file, 2021-07-24]
WOBBLE-RINGS/W-Ring-MIDDLE-V2.STEP
33.0 x 33.0 x 8.50 mm
