cyborgcnc/CYBORGCNC__RRVC3MOD/400x400/LED.CLIP.V2.STL

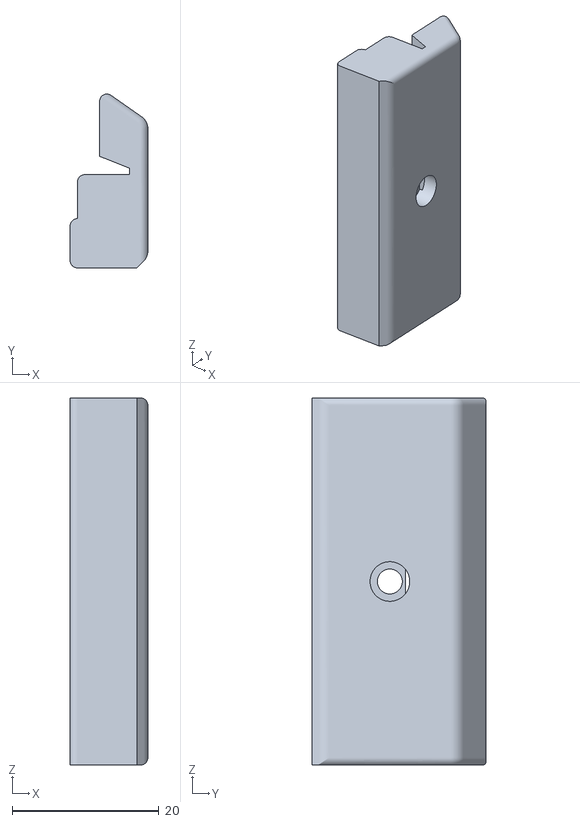
[picture p114: CAD file, 2021-06-16]
400x400/LED.CLIP.V2.STL
10.6 x 23.7 x 50.0
