cyborgcnc/CYBORGCNC__RRVC3MOD/400x400/Panels/Side-Panels.engraved.V2.STEP

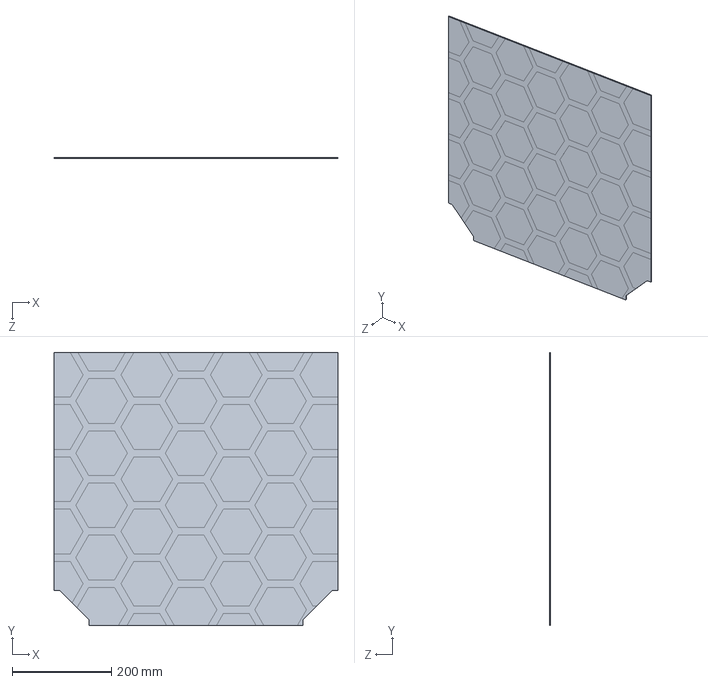
[picture p115: CAD file, 2021-06-25]
400x400/Panels/Side-Panels.engraved.V2.STEP
571.2 x 549.2 x 3.00 mm
