cyborgcnc/CYBORGCNC__RRVC3MOD/500x500/MARCEL-Remix-MODS/Panels/500_Sides.dxf

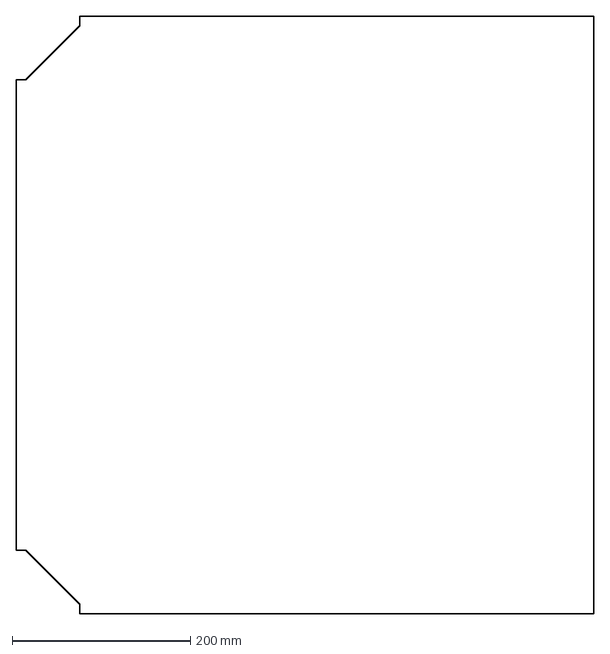
[picture p116: CAD file, 2021-09-10]
500x500/MARCEL-Remix-MODS/Panels/500_Sides.dxf
648.7 x 670.7 mm
