cyborgcnc/CYBORGCNC__RRVC3MOD/Activated-Carbon-Filter/Top-Retainer-Ring.STEP

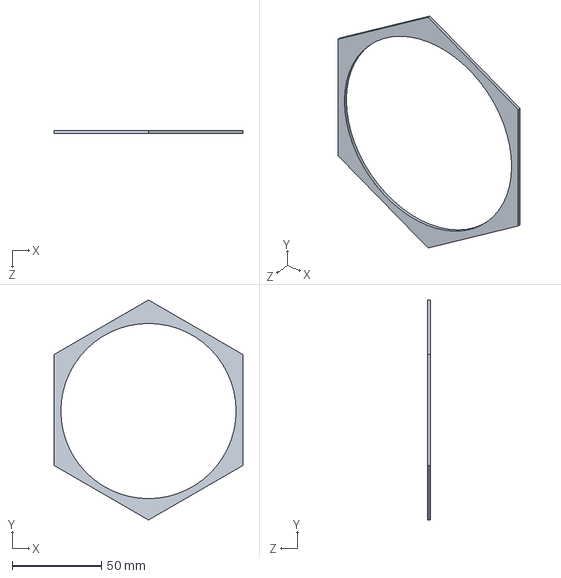
[picture p117: CAD file, 2021-07-02]
Activated-Carbon-Filter/Top-Retainer-Ring.STEP
105.6 x 123.1 x 1.50 mm
