cyborgcnc/CYBORGCNC__RRVC3MOD/Misc/CR-Touch-EVA-Mount.STL

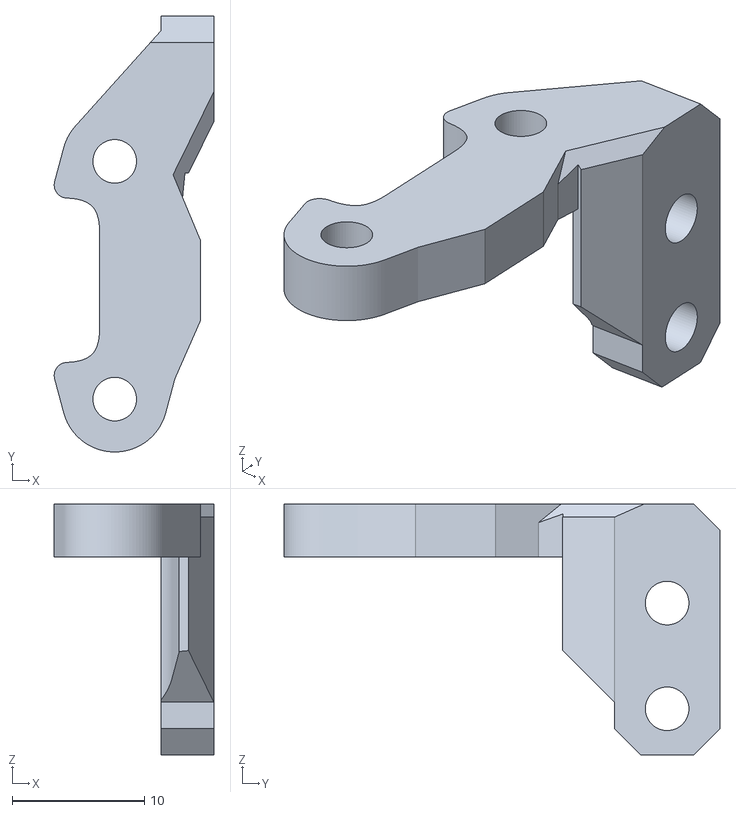
[picture p118: CAD file, 2021-08-24]
Misc/CR-Touch-EVA-Mount.STL
12.1 x 33.0 x 19.0
