cyborgcnc/CYBORGCNC__RRVC3MOD/WOBBLE-RINGS/W-Ring-BOTTOM-V2.STEP

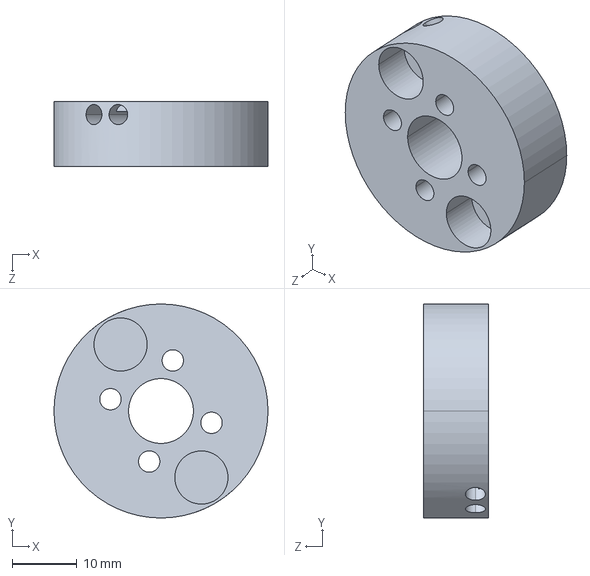
[picture p119: CAD file, 2021-07-24]
WOBBLE-RINGS/W-Ring-BOTTOM-V2.STEP
33.0 x 33.0 x 10.0 mm
