cyborgcnc/CYBORGCNC__RRVC3MOD/400x400/Clip-MidPoint-3mm-3030.STL

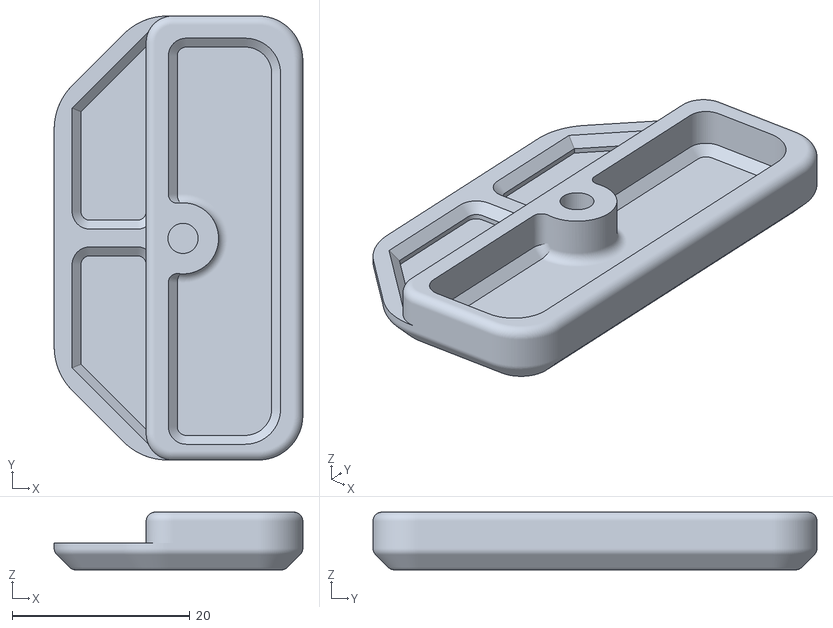
[picture p120: CAD file, 2021-06-16]
400x400/Clip-MidPoint-3mm-3030.STL
28.0 x 50.0 x 6.50
