cyborgcnc/CYBORGCNC__RRVC3MOD/Activated-Carbon-Filter/CF-Mounting-Bracket.STEP

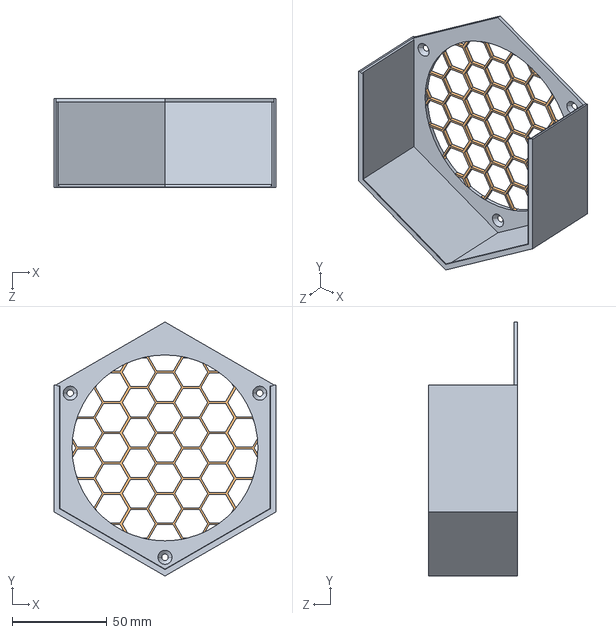
[picture p121: CAD file, 2021-07-02]
Activated-Carbon-Filter/CF-Mounting-Bracket.STEP
117.0 x 133.9 x 47.0 mm
