cyborgcnc/CYBORGCNC__RRVC3MOD/WOBBLE-RINGS/bed_arm_left-right .RING-Version.STL

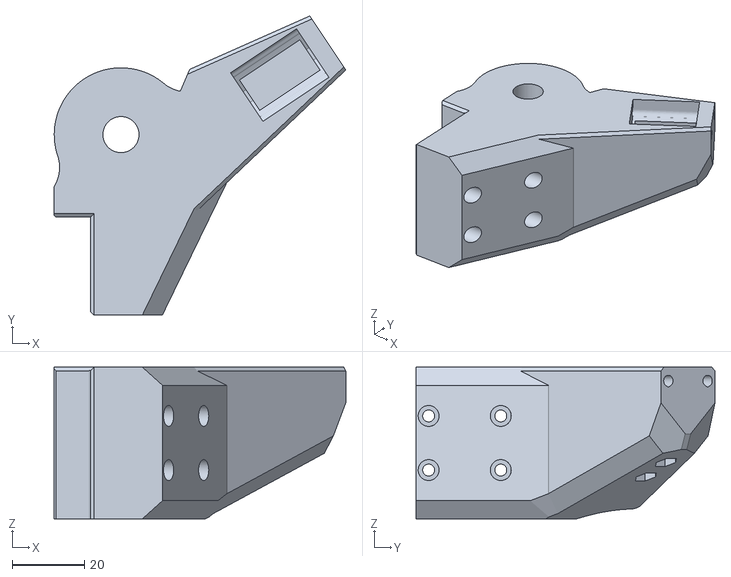
[picture p122: CAD file, 2021-07-24]
WOBBLE-RINGS/bed_arm_left-right .RING-Version.STL
80.8 x 82.9 x 42.0
