cyborgcnc/CYBORGCNC__RRVC3MOD/500x500/MARCEL-Remix-MODS/Top-Lid/500_TopLid_Sides.dxf

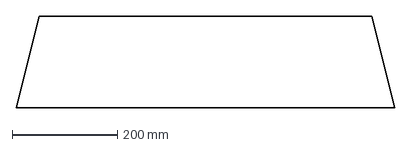
[picture p123: CAD file, 2021-09-10]
500x500/MARCEL-Remix-MODS/Top-Lid/500_TopLid_Sides.dxf
717.5 x 173.9 mm
