cyborgcnc/CYBORGCNC__RRVC3MOD/Activated-Carbon-Filter/Blower-Holder.STEP

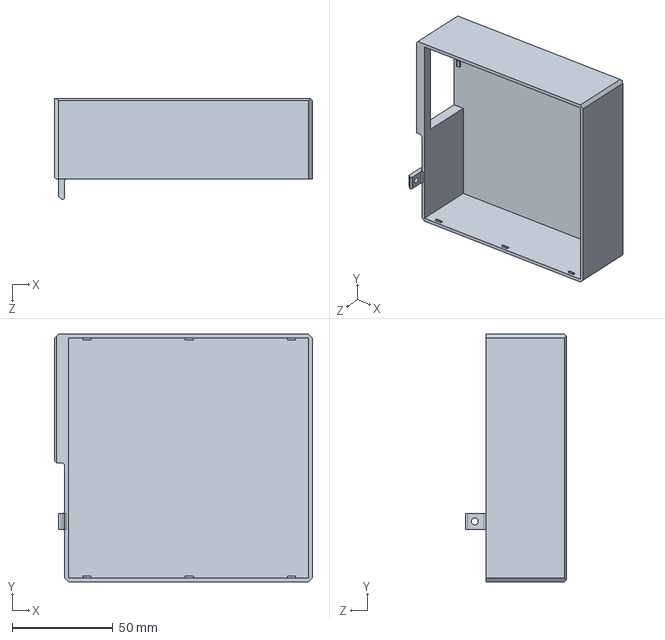
[picture p124: CAD file, 2021-07-02]
Activated-Carbon-Filter/Blower-Holder.STEP
128.2 x 123.2 x 50.1 mm
