cyborgcnc/CYBORGCNC__RRVC3MOD/WOBBLE-RINGS/Bed-Arm-BACK.wobble.STL

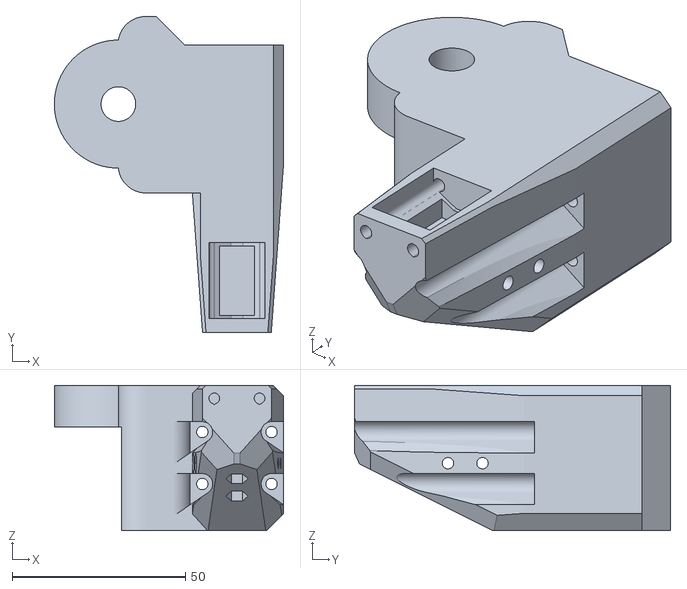
[picture p125: CAD file, 2021-07-24]
WOBBLE-RINGS/Bed-Arm-BACK.wobble.STL
66.3 x 91.3 x 42.0
