cyborgcnc/CYBORGCNC__RRVC3MOD/400x400/TOP-LID/STEP-FILES/Top-Bar-339mm.HALF.STEP

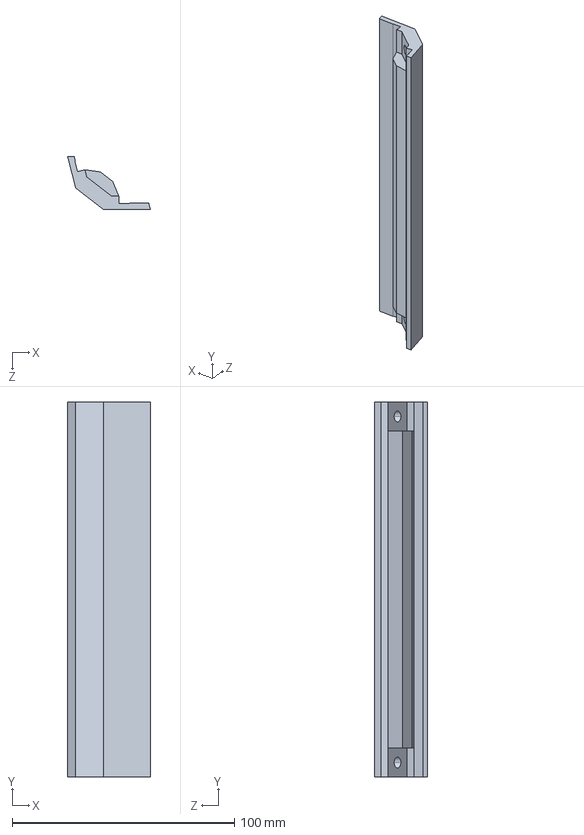
[picture p126: CAD file, 2021-07-08]
400x400/TOP-LID/STEP-FILES/Top-Bar-339mm.HALF.STEP
37.3 x 168.8 x 23.9 mm
