cyborgcnc/CYBORGCNC__RRVC3MOD/Activated-Carbon-Filter/Carbon-Cartridge.STEP

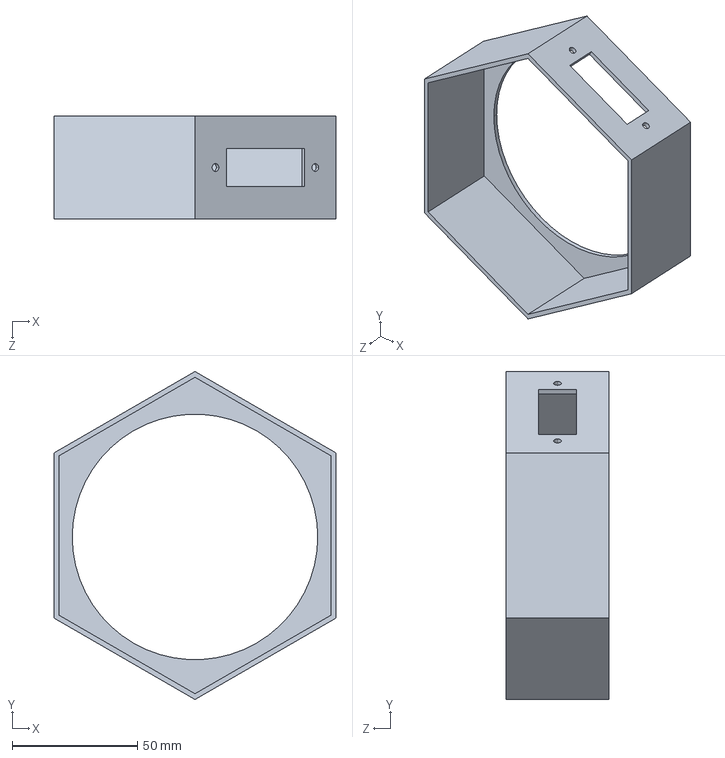
[picture p127: CAD file, 2021-07-02]
Activated-Carbon-Filter/Carbon-Cartridge.STEP
112.4 x 130.9 x 41.0 mm
