cyborgcnc/CYBORGCNC__RRVC3MOD/400x400/TOP-LID/STEP-FILES/Btm-Bar-SIDES.HALF.STEP

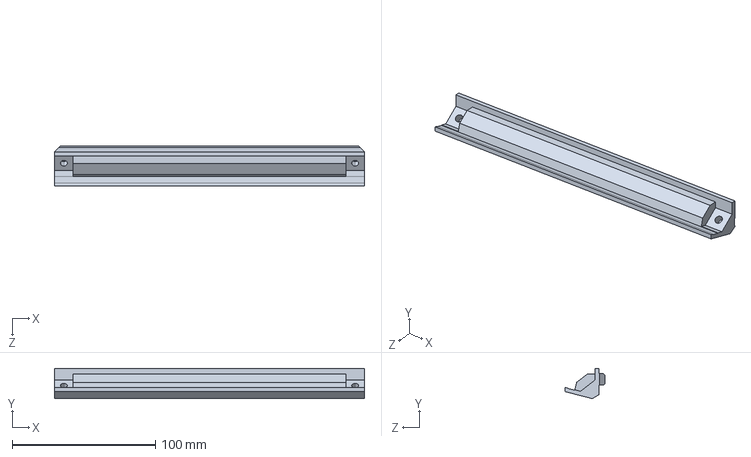
[picture p128: CAD file, 2021-07-08]
400x400/TOP-LID/STEP-FILES/Btm-Bar-SIDES.HALF.STEP
216.3 x 21.2 x 27.9 mm
