cyborgcnc/CYBORGCNC__RRVC3MOD/500x500/MARCEL-Remix-MODS/Top-Lid/500_TopLid_FrontAndBack.dxf

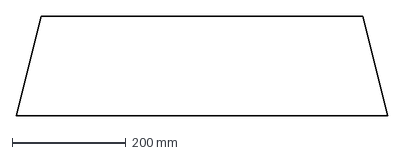
[picture p129: CAD file, 2021-09-10]
500x500/MARCEL-Remix-MODS/Top-Lid/500_TopLid_FrontAndBack.dxf
652.6 x 174.2 mm
