cyborgcnc/CYBORGCNC__RRVC3MOD/Activated-Carbon-Filter/Filter-Mounting-Bracket.STEP

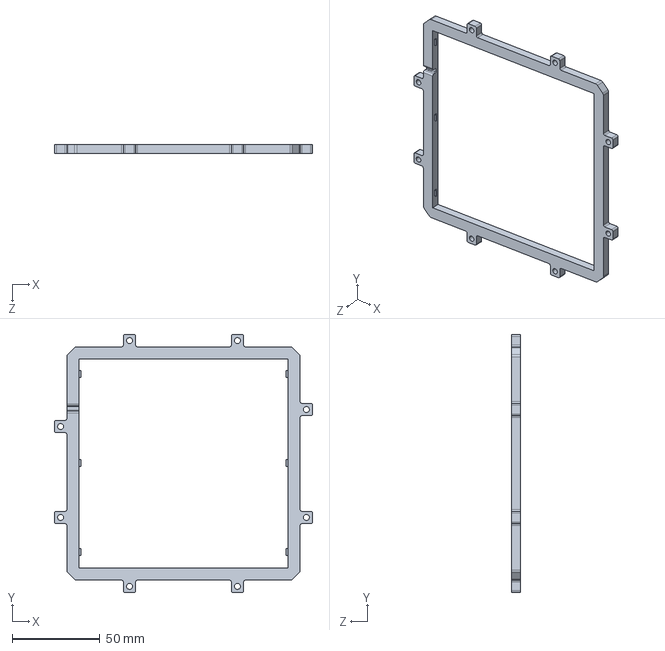
[picture p130: CAD file, 2021-07-02]
Activated-Carbon-Filter/Filter-Mounting-Bracket.STEP
147.2 x 147.2 x 5.00 mm
