cyborgcnc/CYBORGCNC__RRVC3MOD/WOBBLE-RINGS/Bed-Arm-Wobble-Ring.BACK.STEP

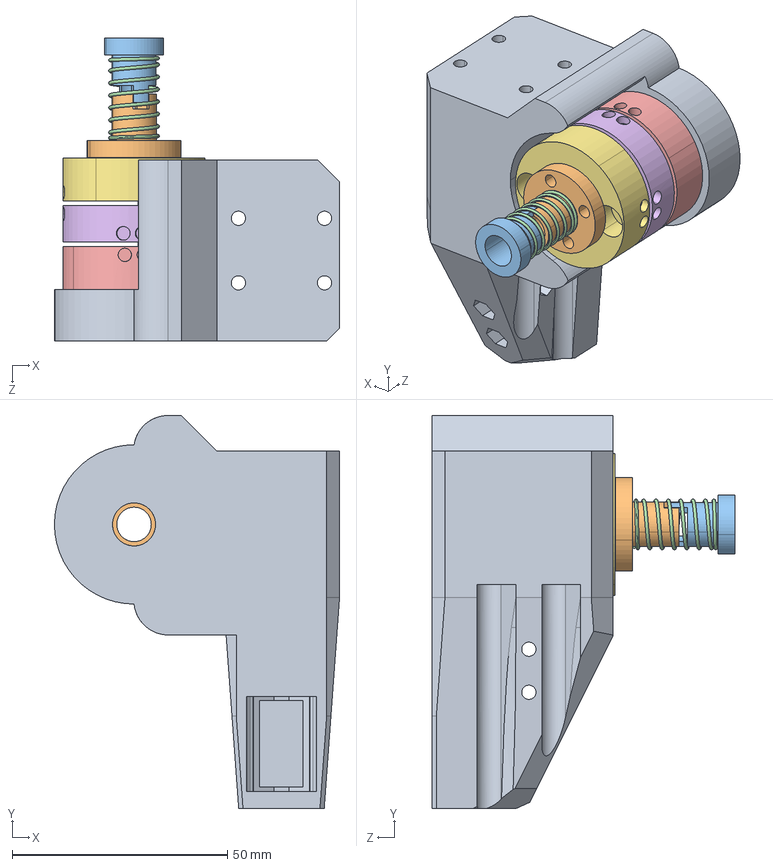
[picture p131: CAD file, 2021-07-24]
WOBBLE-RINGS/Bed-Arm-Wobble-Ring.BACK.STEP
66.3 x 91.3 x 70.4 mm
Bed-Arm-BACK.wobble
TR08
W-Ring-TOP-V2
W-Ring-MIDDLE-V2
W-Ring-BTM-V2
