cyborgcnc/CYBORGCNC__RRVC3MOD/Activated-Carbon-Filter/HEPA-Bracket.STEP

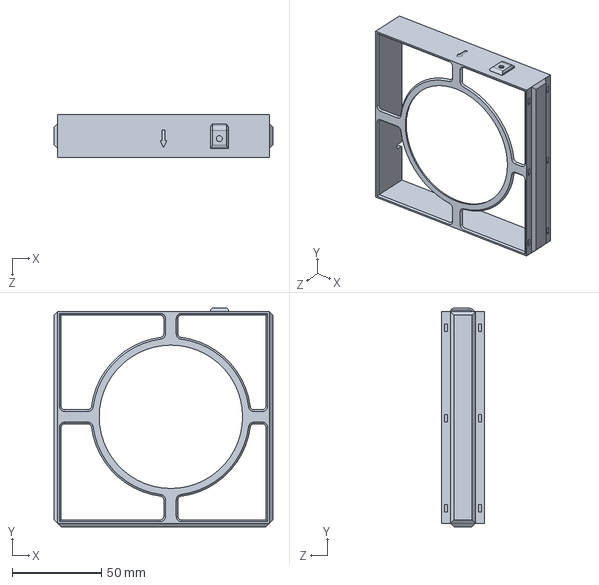
[picture p132: CAD file, 2021-07-02]
Activated-Carbon-Filter/HEPA-Bracket.STEP
123.0 x 123.0 x 24.0 mm
