cyborgcnc/CYBORGCNC__RRVC3MOD/500x500/MARCEL-Remix-MODS/Top-Lid/500_Btm-Bar-SIDES.HALF.stl

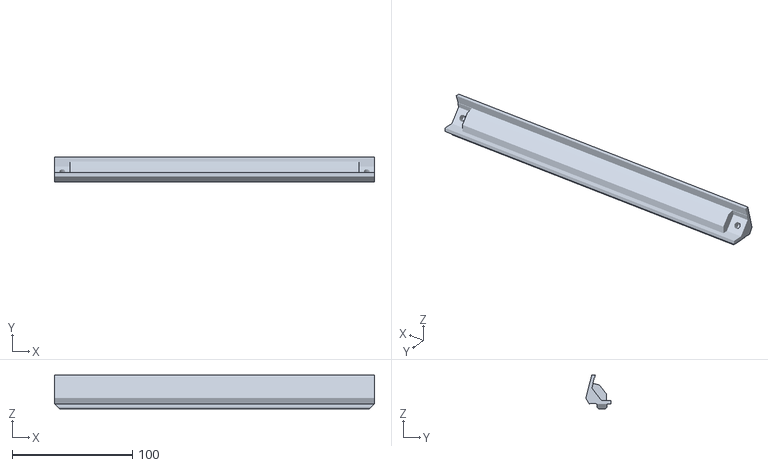
[picture p133: CAD file, 2021-09-10]
500x500/MARCEL-Remix-MODS/Top-Lid/500_Btm-Bar-SIDES.HALF.stl
266.2 x 21.2 x 27.9
