cyborgcnc/CYBORGCNC__RRVC3MOD/500x500/MARCEL-Remix-MODS/Top-Lid/Hinge-Back-BTMV3.STL

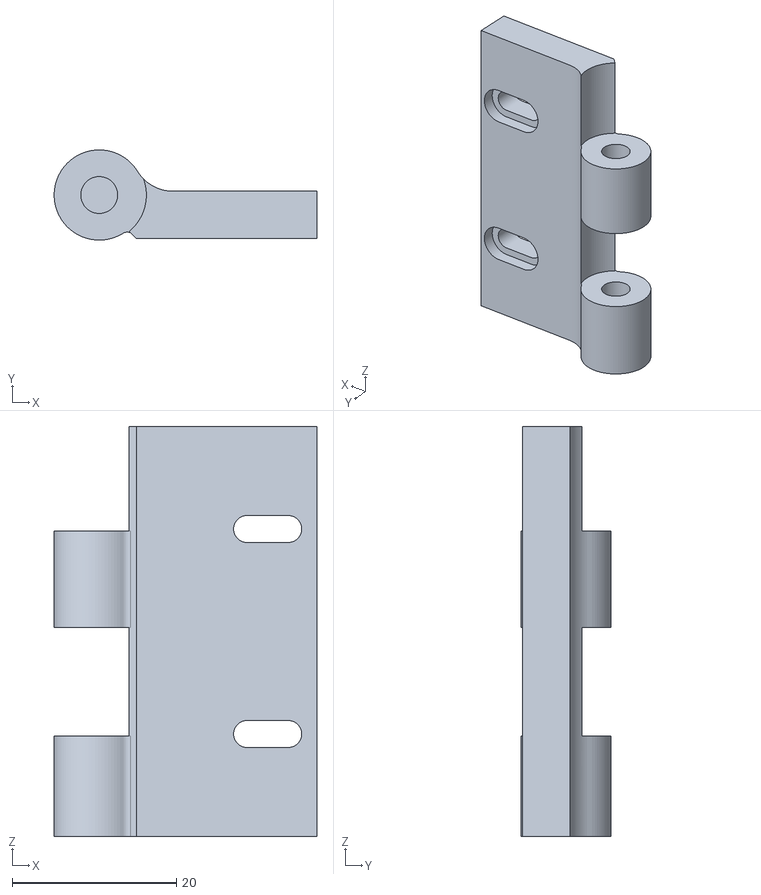
[picture p134: CAD file, 2021-08-09]
500x500/MARCEL-Remix-MODS/Top-Lid/Hinge-Back-BTMV3.STL
32.0 x 11.0 x 50.0
