cyborgcnc/CYBORGCNC__RRVC3MOD/500x500/MARCEL-Remix-MODS/Top-Lid/Hinge-Back-TOPV3.STL

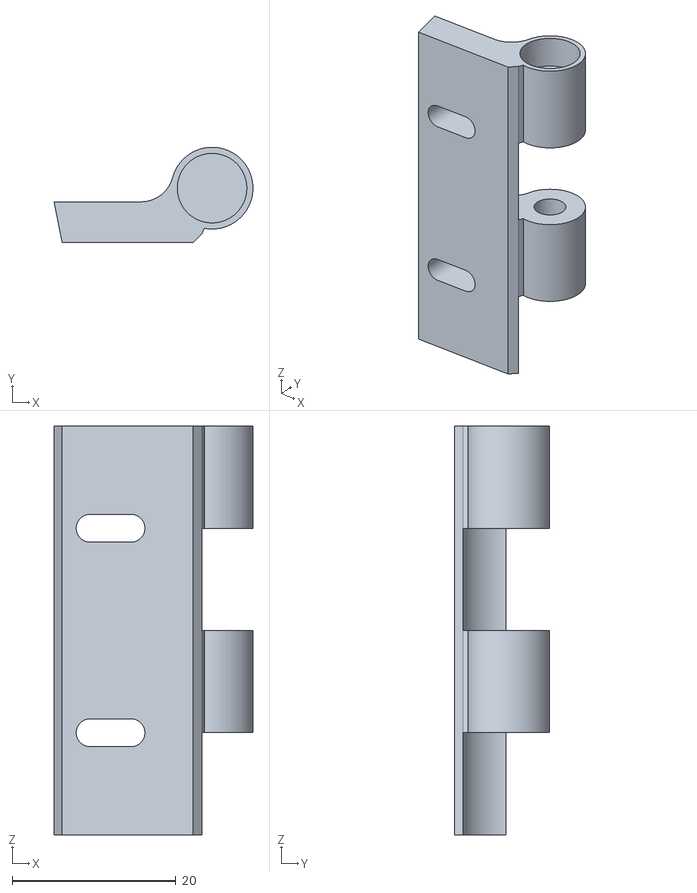
[picture p135: CAD file, 2021-08-09]
500x500/MARCEL-Remix-MODS/Top-Lid/Hinge-Back-TOPV3.STL
24.3 x 11.7 x 50.0
