cyborgcnc/CYBORGCNC__RRVC3MOD/500x500/MARCEL-Remix-MODS/Top-Lid/BTM-Clip-Joiners.STL

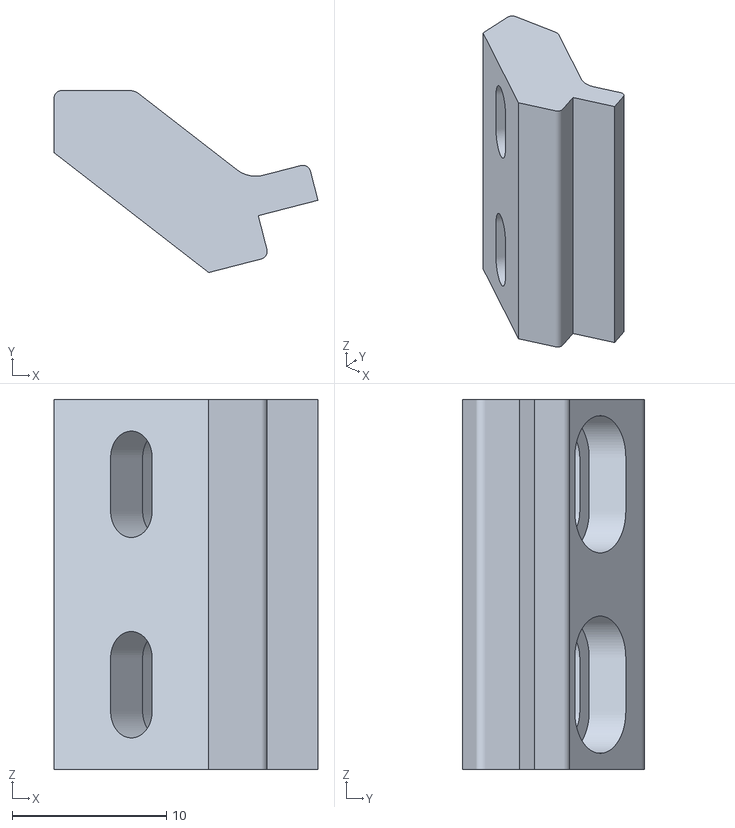
[picture p136: CAD file, 2021-06-28]
500x500/MARCEL-Remix-MODS/Top-Lid/BTM-Clip-Joiners.STL
17.1 x 11.8 x 24.0
