cyborgcnc/CYBORGCNC__RRVC3MOD/500x500/MARCEL-Remix-MODS/Top-Lid/OUTSIDE-Top-Clipv2.STL

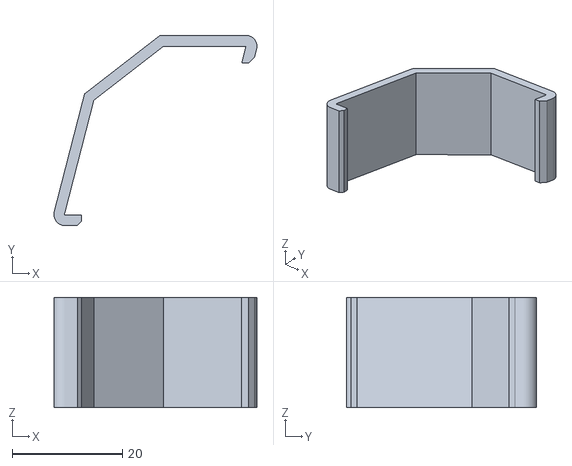
[picture p137: CAD file, 2021-06-25]
500x500/MARCEL-Remix-MODS/Top-Lid/OUTSIDE-Top-Clipv2.STL
36.8 x 34.5 x 20.0
