cyborgcnc/CYBORGCNC__RRVC3MOD/400x400/TOP-LID/STEP-FILES/README.md

# STEP FILES

These are the STEp files for the top lid for my 400mm Vcore3.  I am not sure at this time I will be remixing for all the other versions (just no time), but feel free to modify as needed.

I have also provided an Assembly file, so that you can see how all the parts fit together.
